oresat/oresat-proto-card/I2C-protection-sims/I2Cprotection.asc

C1: cap; .1µ
M1: pmos
R1: res; 10k
R2: res; 100k
R3: res; 1Meg
U1: LTC1441
V1: voltage; 1.2
V2: voltage; 3.3
V3: voltage; PULSE(0 3.3 0 0 0 5u 10u)
Named nets: 0, Vref, V+, Signal
.tran .001
