oresat/oresat-proto-card/a8-proto-card/cad-files/Connectors.kicad_sch

## KiCad design a8-proto-card/cad-files/Connectors.kicad_sch (2021-11-15)

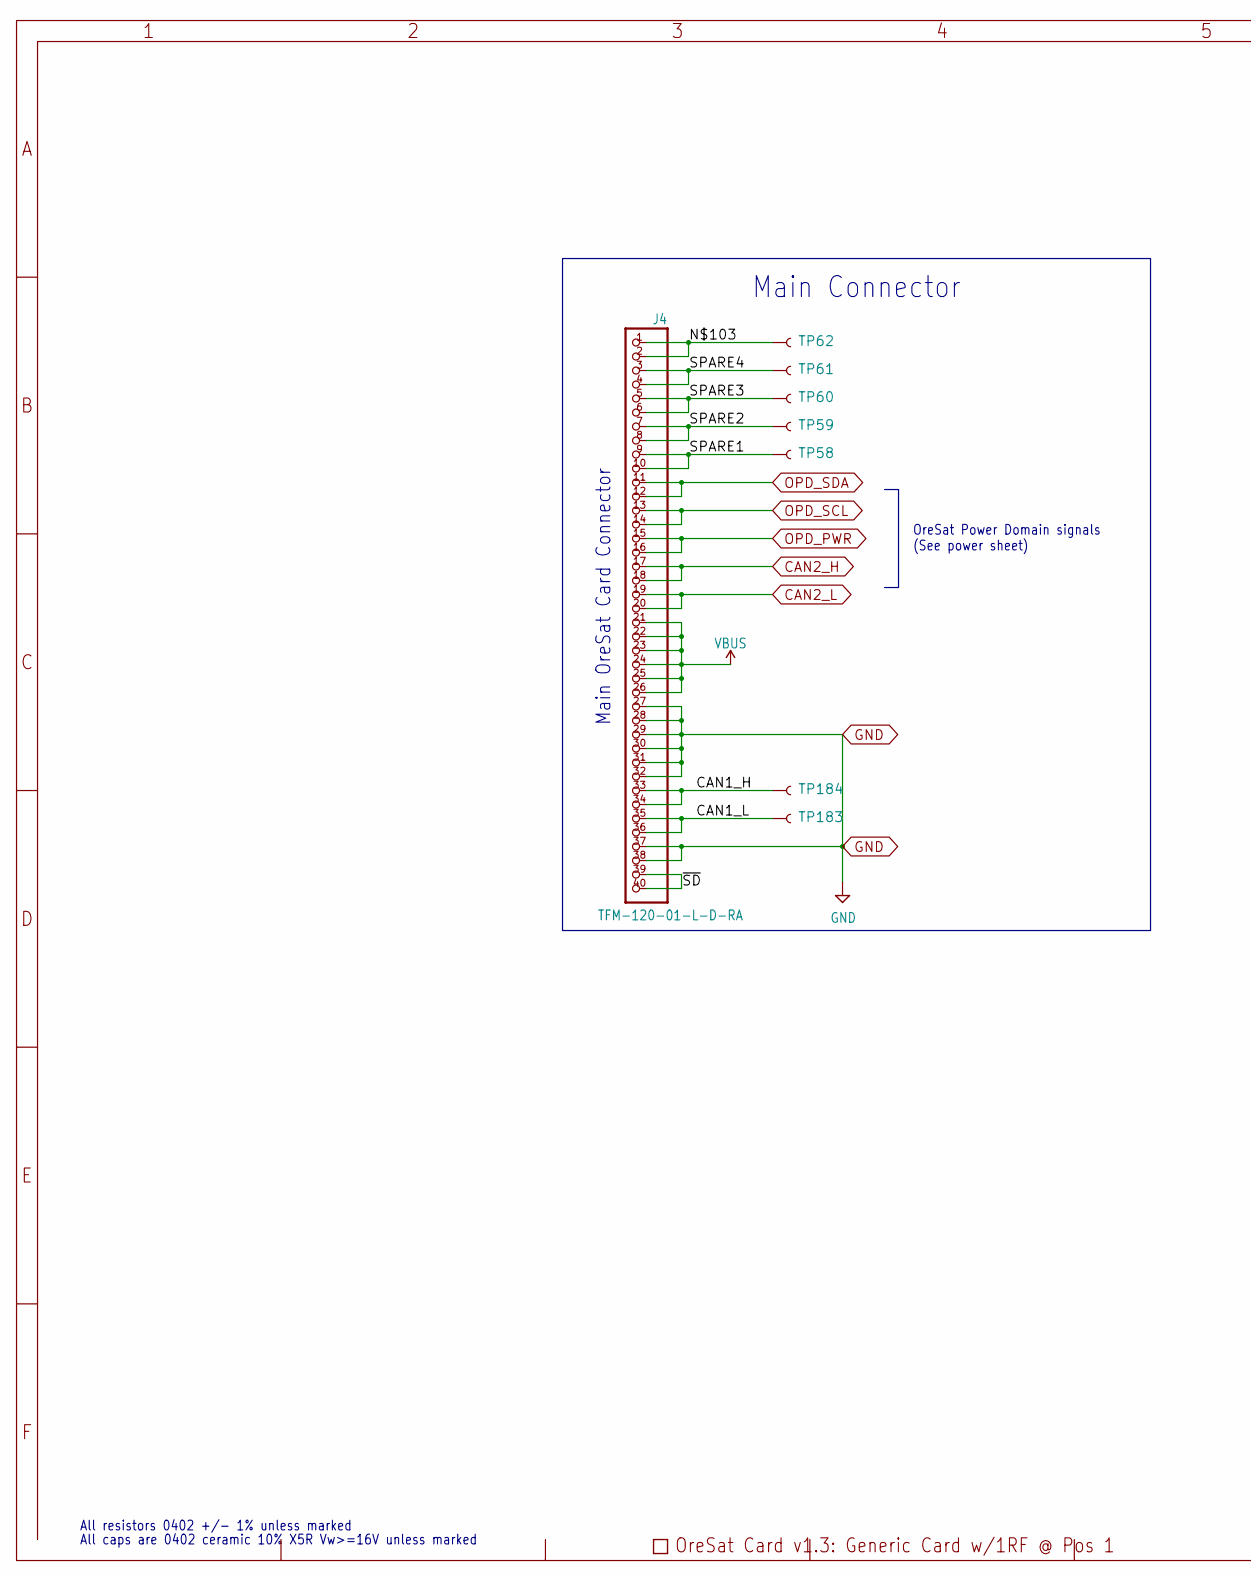
[picture p10: schematic Connectors.kicad_sch, part in row 1, column 1]

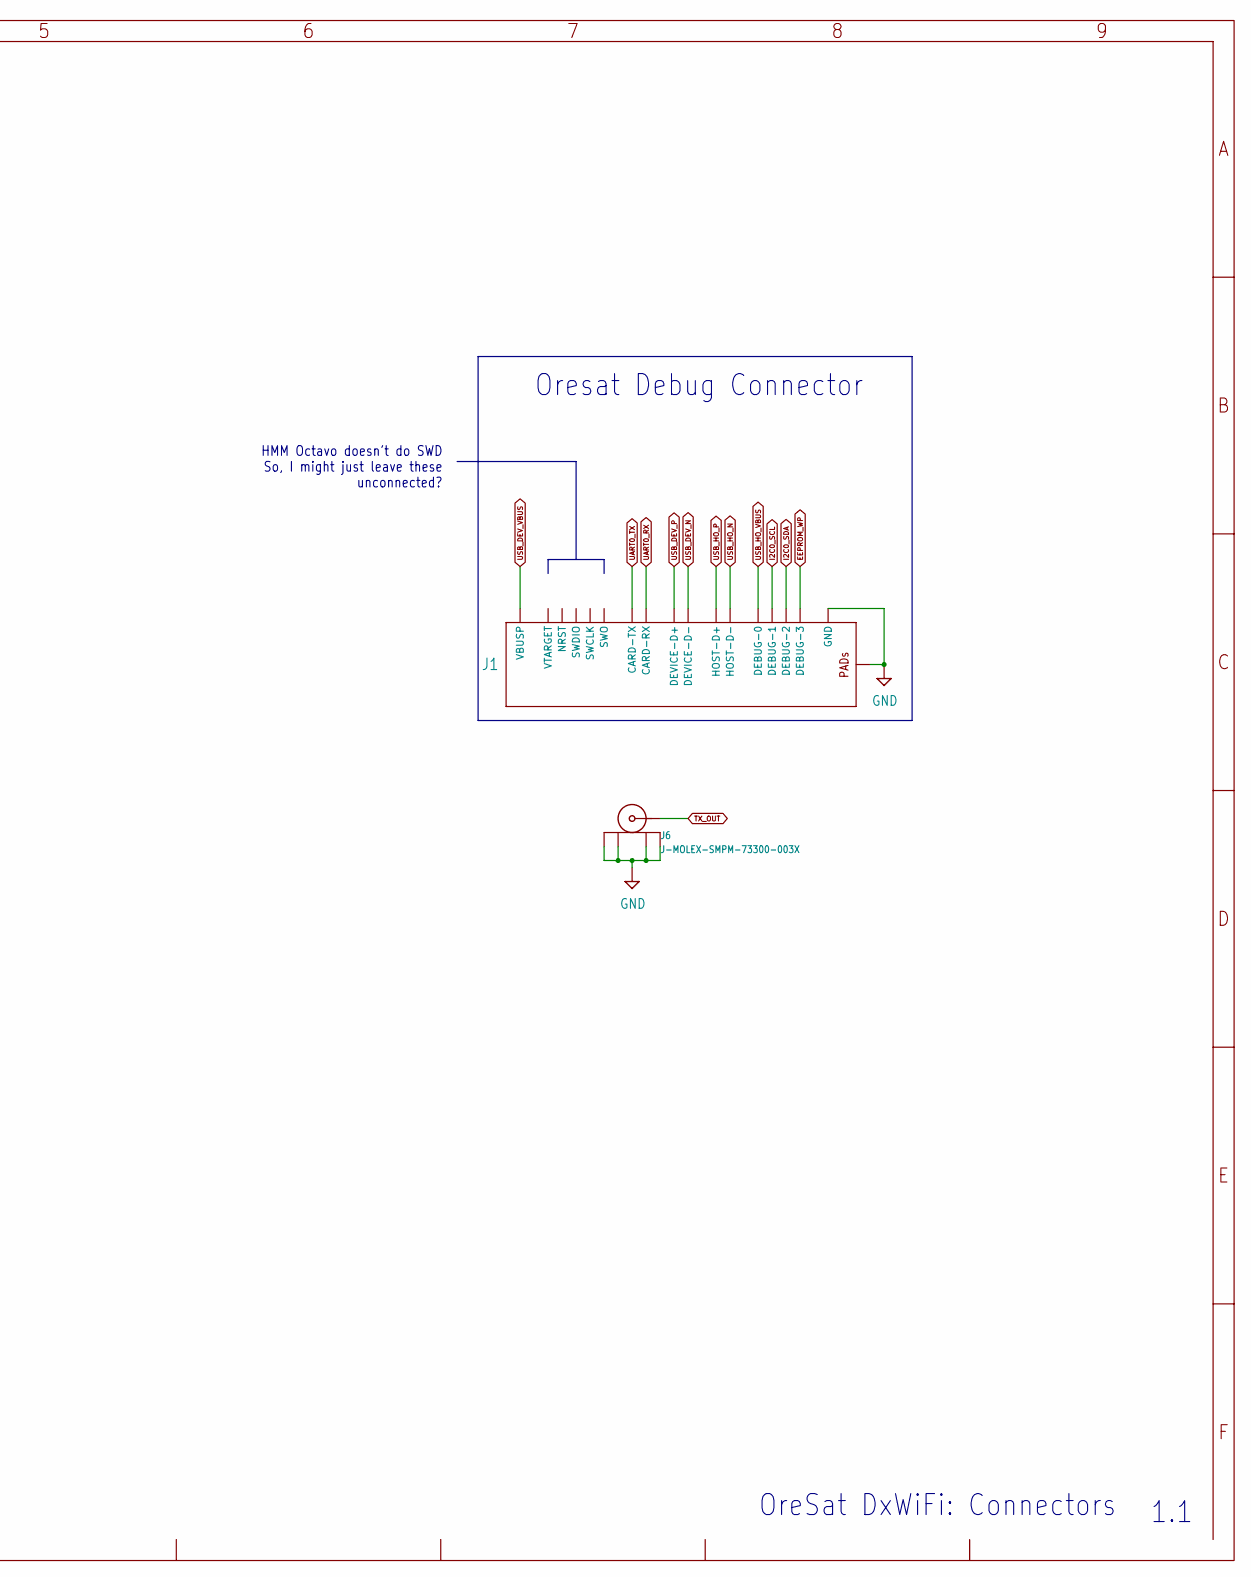
[picture p11: schematic Connectors.kicad_sch, part in row 1, column 2]

Parts:
J1: ORESAT-DEBUG-CONNECTOR-CARD; TE_2-1734592-0
J4: TFM-120-01-L-D-RA; J-SAMTEC-TFM-120-X1-XXX-D-RA
J6: J-MOLEX-SMPM-73300-003X; J-MOLEX-SMPM-073300-003X
PCB1: ORESAT-CARD-V1.3-GENERIC-1RF-POS1
TP58, TP59, TP60, TP61, TP62, TP183, TP184: TEST-POINT3X4; PAD.03X.04

Connections:
CAN1_H: J4.33, J4.34, TP184.1
CAN1_L: J4.35, J4.36, TP183.1
CAN2_H: J4.17, J4.18
CAN2_L: J4.19, J4.20
EEPROM_WP: J1.20 (DEBUG-3)
GND: J1.3 (GND), J1.6 (GND), J1.9 (GND), J1.PAD1 (PAD), J1.PAD2 (PAD), J4.27, J4.28, J4.29, J4.30, J4.31, J4.32, J4.37, J4.38, J6.P$1 (SHIELD3), J6.P$2 (SHIELD2), J6.P$3 (SHIELD1), J6.P$4 (SHIELD)
I2C0_SCL: J1.18 (DEBUG-1)
I2C0_SDA: J1.19 (DEBUG-2)
unnamed: J4.1, J4.2, TP62.1
OPD_PWR: J4.15, J4.16
OPD_SCL: J4.13, J4.14
OPD_SDA: J4.11, J4.12
SPARE1: J4.9, J4.10, TP58.1
SPARE2: J4.7, J4.8, TP59.1
SPARE3: J4.5, J4.6, TP60.1
SPARE4: J4.3, J4.4, TP61.1
TX_OUT: J6.RF (CENTER)
UART0_RX: J1.12 (CARD-RX)
UART0_TX: J1.13 (CARD-TX)
USB_DEV_N: J1.5 (DEVICE-D-)
USB_DEV_P: J1.4 (DEVICE-D+)
USB_DEV_VBUS: J1.1 (VBUSP), J1.2 (VBUSP)
USB_HO_N: J1.8 (HOST-D-)
USB_HO_P: J1.7 (HOST-D+)
USB_HO_VBUS: J1.17 (DEBUG-0)
VBUS: J4.21, J4.22, J4.23, J4.24, J4.25, J4.26
~SD: J4.39, J4.40

Notes on the sheet:
Main OreSat Card Connector
Oresat Debug Connector
OreSat DxWiFi: Connectors
HMM Octavo doesn't do SWD So, I might just leave these unconnected?
Main Connector
1.1
OreSat Power Domain signals (See power sheet)
All caps are 0402 ceramic 10% X5R Vw>=16V unless marked
All resistors 0402 +/- 1% unless marked
