oresat/oresat-proto-card/a8-proto-card/cad-files/OSD3358_PWR,_ETC._%3a_SIP_A,_E,_F.kicad_sch

## KiCad design a8-proto-card/cad-files/OSD3358_PWR,_ETC._%3a_SIP_A,_E,_F.kicad_sch (2021-11-15)

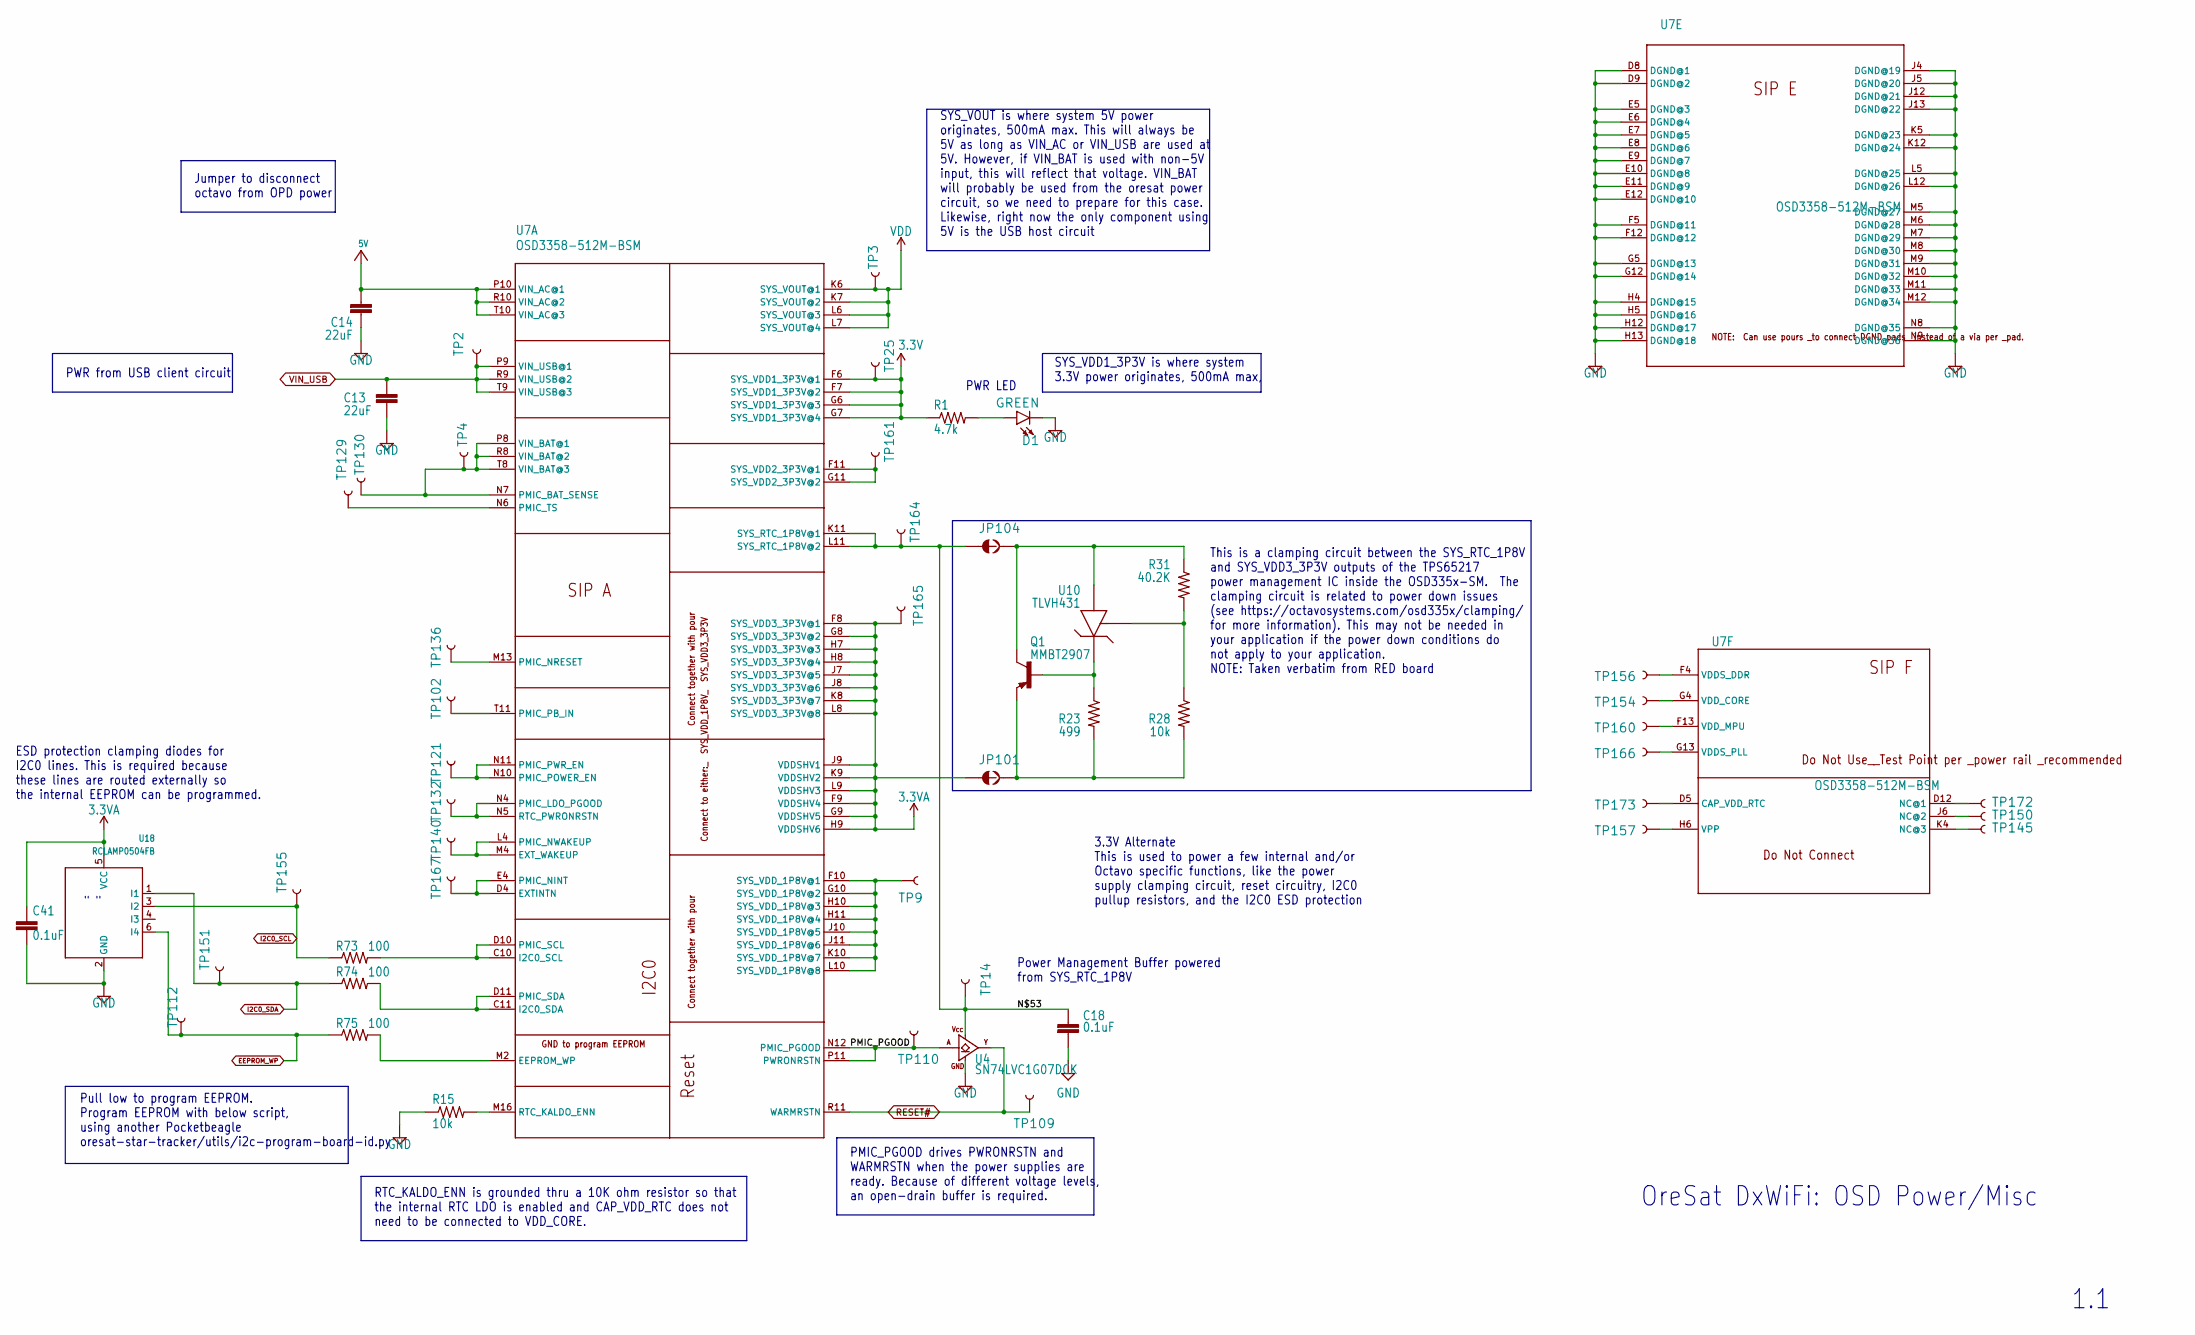
[picture p12: schematic OSD3358_PWR,_ETC._%3a_SIP_A,_E,_F.kicad_sch]

Parts:
C13, C14: 22uF; C1210
C18, C41: 0.1uF; .0603-A
D1: 150060VS55040; LED-0603
JP101, JP104: JUMPER-SMT_2_NC_TRACE_SILK; SMT-JUMPER_2_NC_TRACE_SILK
Q1: MMBT2907; SOT23-BEC
R1: 4.7k; .0603-A
R15, R28: 10k; .0603-A
R23: 499; .0603-A
R31: 40.2K; .0603-A
R73, R74, R75: 100; .0603-A
TP2, TP3, TP4, TP9, TP14, TP25, TP102, TP109, TP110, TP112, TP121, TP129, TP130, TP132, TP136, TP140, TP145, TP150, TP151, TP154, TP155, TP156, TP157, TP160, TP161, TP164, TP165, TP166, TP167, TP172, TP173: TEST-POINT3X4; PAD.03X.04
U4: SN74LVC1G07DCK; C70(TI-DCK)
U7: OSD3358-512M-BSM; OSD335X-BGA-256
U10: TLVH431; SOT23-3
U18: RCLAMP0504FB; SC70-6

Connections:
3.3V: R1.1, TP25.1, U7.F6 (SYS_VDD1_3P3V@1), U7.F7 (SYS_VDD1_3P3V@2), U7.G6 (SYS_VDD1_3P3V@3), U7.G7 (SYS_VDD1_3P3V@4)
3.3VA: C41.1, JP101.1, TP165.1, U7.F8 (SYS_VDD3_3P3V@1), U7.F9 (VDDSHV4), U7.G8 (SYS_VDD3_3P3V@2), U7.G9 (VDDSHV5), U7.H7 (SYS_VDD3_3P3V@3), U7.H8 (SYS_VDD3_3P3V@4), U7.H9 (VDDSHV6), U7.J7 (SYS_VDD3_3P3V@5), U7.J8 (SYS_VDD3_3P3V@6), U7.J9 (VDDSHV1), U7.K8 (SYS_VDD3_3P3V@7), U7.K9 (VDDSHV2), U7.L8 (SYS_VDD3_3P3V@8), U7.L9 (VDDSHV3), U18.5 (VCC)
5V: C14.1, U7.P10 (VIN_AC@1), U7.R10 (VIN_AC@2), U7.T10 (VIN_AC@3)
EEPROM_WP: R75.1, TP112.1, U18.6 (I4)
GND: C13.2, C14.2, C18.2, C41.2, D1.C, R15.1, U4.3 (GND), U7.D8 (DGND@1), U7.D9 (DGND@2), U7.E5 (DGND@3), U7.E6 (DGND@4), U7.E7 (DGND@5), U7.E8 (DGND@6), U7.E9 (DGND@7), U7.E10 (DGND@8), U7.E11 (DGND@9), U7.E12 (DGND@10), U7.F5 (DGND@11), U7.F12 (DGND@12), U7.G5 (DGND@13), U7.G12 (DGND@14), U7.H4 (DGND@15), U7.H5 (DGND@16), U7.H12 (DGND@17), U7.H13 (DGND@18), U7.J4 (DGND@19), U7.J5 (DGND@20), U7.J12 (DGND@21), U7.J13 (DGND@22), U7.K5 (DGND@23), U7.K12 (DGND@24), U7.L5 (DGND@25), U7.L12 (DGND@26), U7.M5 (DGND@27), U7.M6 (DGND@28), U7.M7 (DGND@29), U7.M8 (DGND@30), U7.M9 (DGND@31), U7.M10 (DGND@32), U7.M11 (DGND@33), U7.M12 (DGND@34), U7.N8 (DGND@35), U7.N9 (DGND@36), U18.2 (GND)
I2C0_SCL: R73.1, TP155.1, U18.3 (I2)
I2C0_SDA: R74.1, TP151.1, U18.1 (I1)
unnamed: C18.1, JP104.1, TP14.1, TP164.1, U4.5 (VCC), U7.K11 (SYS_RTC_1P8V@1), U7.L11 (SYS_RTC_1P8V@2)
unnamed: D1.A, R1.2
unnamed: JP101.2, Q1.E, R23.2, R28.2
unnamed: JP104.2, Q1.C, R31.1, U10.3 (ANODE)
unnamed: Q1.B, R23.1, U10.2 (CATHODE)
unnamed: R15.2, U7.M16 (RTC_KALDO_ENN)
unnamed: R28.1, R31.2, U10.1 (REF)
unnamed: R73.2, U7.C10 (I2C0_SCL), U7.D10 (PMIC_SCL)
unnamed: R74.2, U7.C11 (I2C0_SDA), U7.D11 (PMIC_SDA)
unnamed: R75.2, U7.M2 (EEPROM_WP)
unnamed: TP9.1, U7.F10 (SYS_VDD_1P8V@1), U7.G10 (SYS_VDD_1P8V@2), U7.H10 (SYS_VDD_1P8V@3), U7.H11 (SYS_VDD_1P8V@4), U7.J10 (SYS_VDD_1P8V@5), U7.J11 (SYS_VDD_1P8V@6), U7.K10 (SYS_VDD_1P8V@7), U7.L10 (SYS_VDD_1P8V@8)
unnamed: TP102.1, U7.T11 (PMIC_PB_IN)
unnamed: TP121.1, U7.N10 (PMIC_POWER_EN), U7.N11 (PMIC_PWR_EN)
unnamed: TP129.1, U7.N6 (PMIC_TS)
unnamed: TP4.1, TP130.1, U7.N7 (PMIC_BAT_SENSE), U7.P8 (VIN_BAT@1), U7.R8 (VIN_BAT@2), U7.T8 (VIN_BAT@3)
unnamed: TP132.1, U7.N4 (PMIC_LDO_PGOOD), U7.N5 (RTC_PWRONRSTN)
unnamed: TP136.1, U7.M13 (PMIC_NRESET)
unnamed: TP140.1, U7.L4 (PMIC_NWAKEUP), U7.M4 (EXT_WAKEUP)
unnamed: TP145.1, U7.K4 (NC@3)
unnamed: TP150.1, U7.J6 (NC@2)
unnamed: TP154.1, U7.G4 (VDD_CORE)
unnamed: TP156.1, U7.F4 (VDDS_DDR)
unnamed: TP157.1, U7.H6 (VPP)
unnamed: TP160.1, U7.F13 (VDD_MPU)
unnamed: TP161.1, U7.F11 (SYS_VDD2_3P3V@1), U7.G11 (SYS_VDD2_3P3V@2)
unnamed: TP166.1, U7.G13 (VDDS_PLL)
unnamed: TP167.1, U7.D4 (EXTINTN), U7.E4 (PMIC_NINT)
unnamed: TP172.1, U7.D12 (NC@1)
unnamed: TP173.1, U7.D5 (CAP_VDD_RTC)
PMIC_PGOOD: TP110.1, U4.2 (A), U7.N12 (PMIC_PGOOD), U7.P11 (PWRONRSTN)
RESET#: TP109.1, U4.4 (Y), U7.R11 (WARMRSTN)
VDD: TP3.1, U7.K6 (SYS_VOUT@1), U7.K7 (SYS_VOUT@2), U7.L6 (SYS_VOUT@3), U7.L7 (SYS_VOUT@4)
VIN_USB: C13.1, TP2.1, U7.P9 (VIN_USB@1), U7.R9 (VIN_USB@2), U7.T9 (VIN_USB@3)

Notes on the sheet:
Pull low to program EEPROM. Program EEPROM with below script, using another Pocketbeagle oresat-star-tracker/utils/i2c-program-board-id.py
ESD protection clamping diodes for I2C0 lines. This is required because these lines are routed externally so the internal EEPROM can be programmed.
This is a clamping circuit between the SYS_RTC_1P8V and SYS_VDD3_3P3V outputs of the TPS65217 power management IC inside the OSD335x-SM. The clamping circuit is related to power down issues (see https://octavosystems.com/osd335x/clamping/ for more information). This may not be needed in your applic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
RTC_KALDO_ENN is grounded thru a 10K ohm resistor so that the internal RTC LDO is enabled and CAP_VDD_RTC does not need to be connected to VDD_CORE.
3.3V Alternate This is used to power a few internal and/or Octavo specific functions, like the power supply clamping circuit, reset circuitry, I2C0 pullup resistors, and the I2C0 ESD protection
Jumper to disconnect octavo from OPD power
SYS_VDD1_3P3V is where system 3.3V power originates, 500mA max,
" "
PMIC_PGOOD drives PWRONRSTN and WARMRSTN when the power supplies are ready. Because of different voltage levels, an open-drain buffer is required.
OreSat DxWiFi: OSD Power/Misc
SYS_VOUT is where system 5V power originates, 500mA max. This will always be 5V as long as VIN_AC or VIN_USB are used at 5V. However, if VIN_BAT is used with non-5V input, this will reflect that voltage. VIN_BAT will probably be used from the oresat power circuit, so we need to prepare for this cas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
Power Management Buffer powered from SYS_RTC_1P8V
PWR from USB client circuit
1.1
PWR LED
