oresat/oresat-proto-card/a8-proto-card/cad-files/OSD3358_SD,_eMMC%3a_SIP_C,_D.kicad_sch

## KiCad design a8-proto-card/cad-files/OSD3358_SD,_eMMC%3a_SIP_C,_D.kicad_sch (2021-11-15)

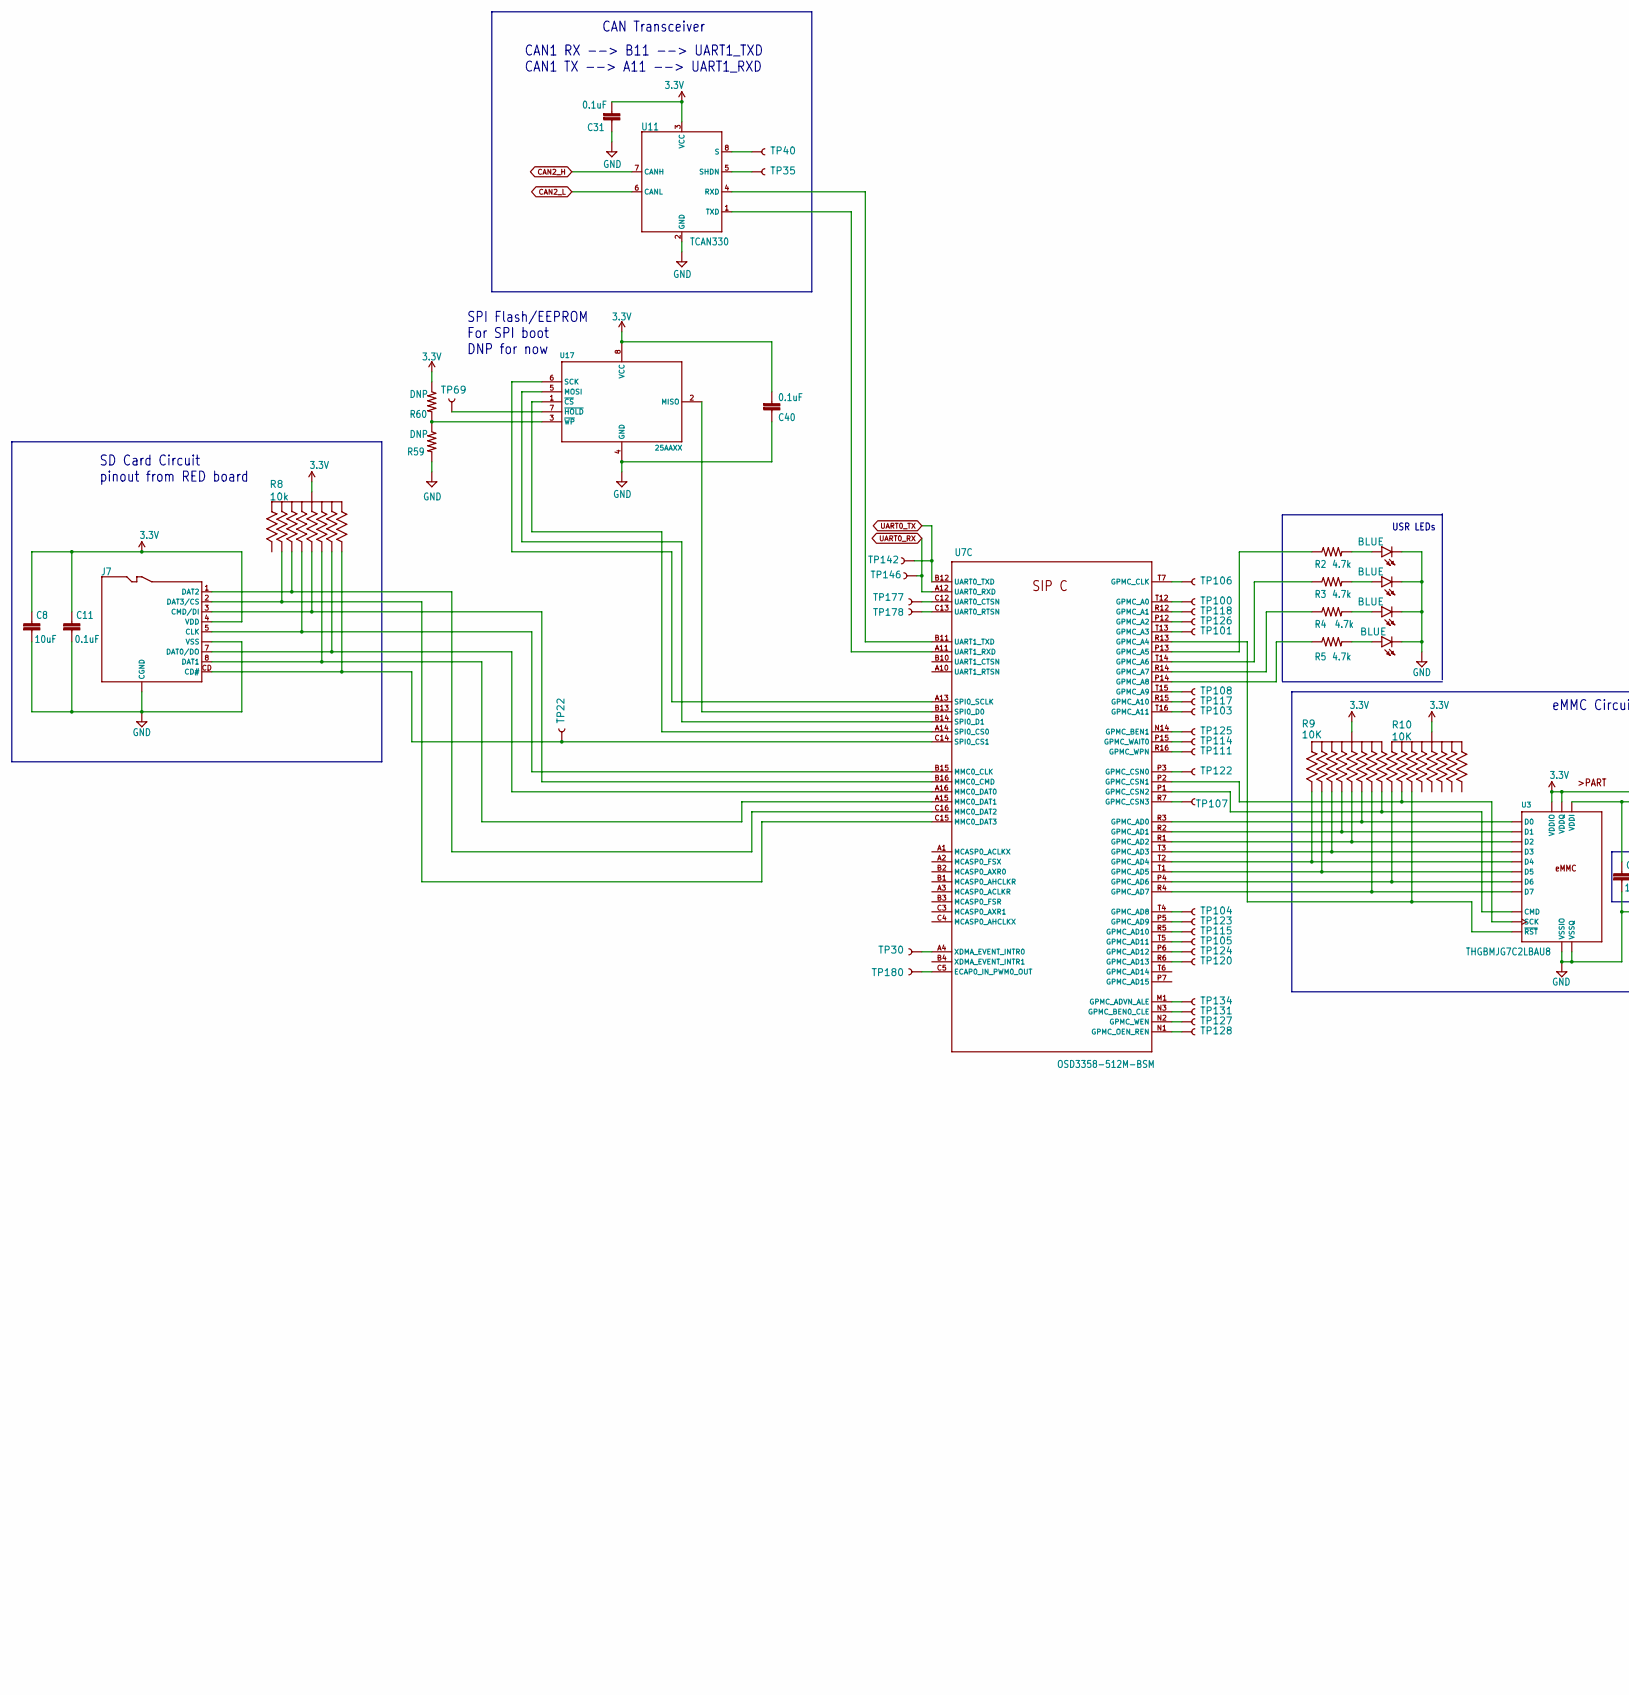
[picture p13: schematic OSD3358_SD,_eMMC%3a_SIP_C,_D.kicad_sch, part in row 1, column 1]

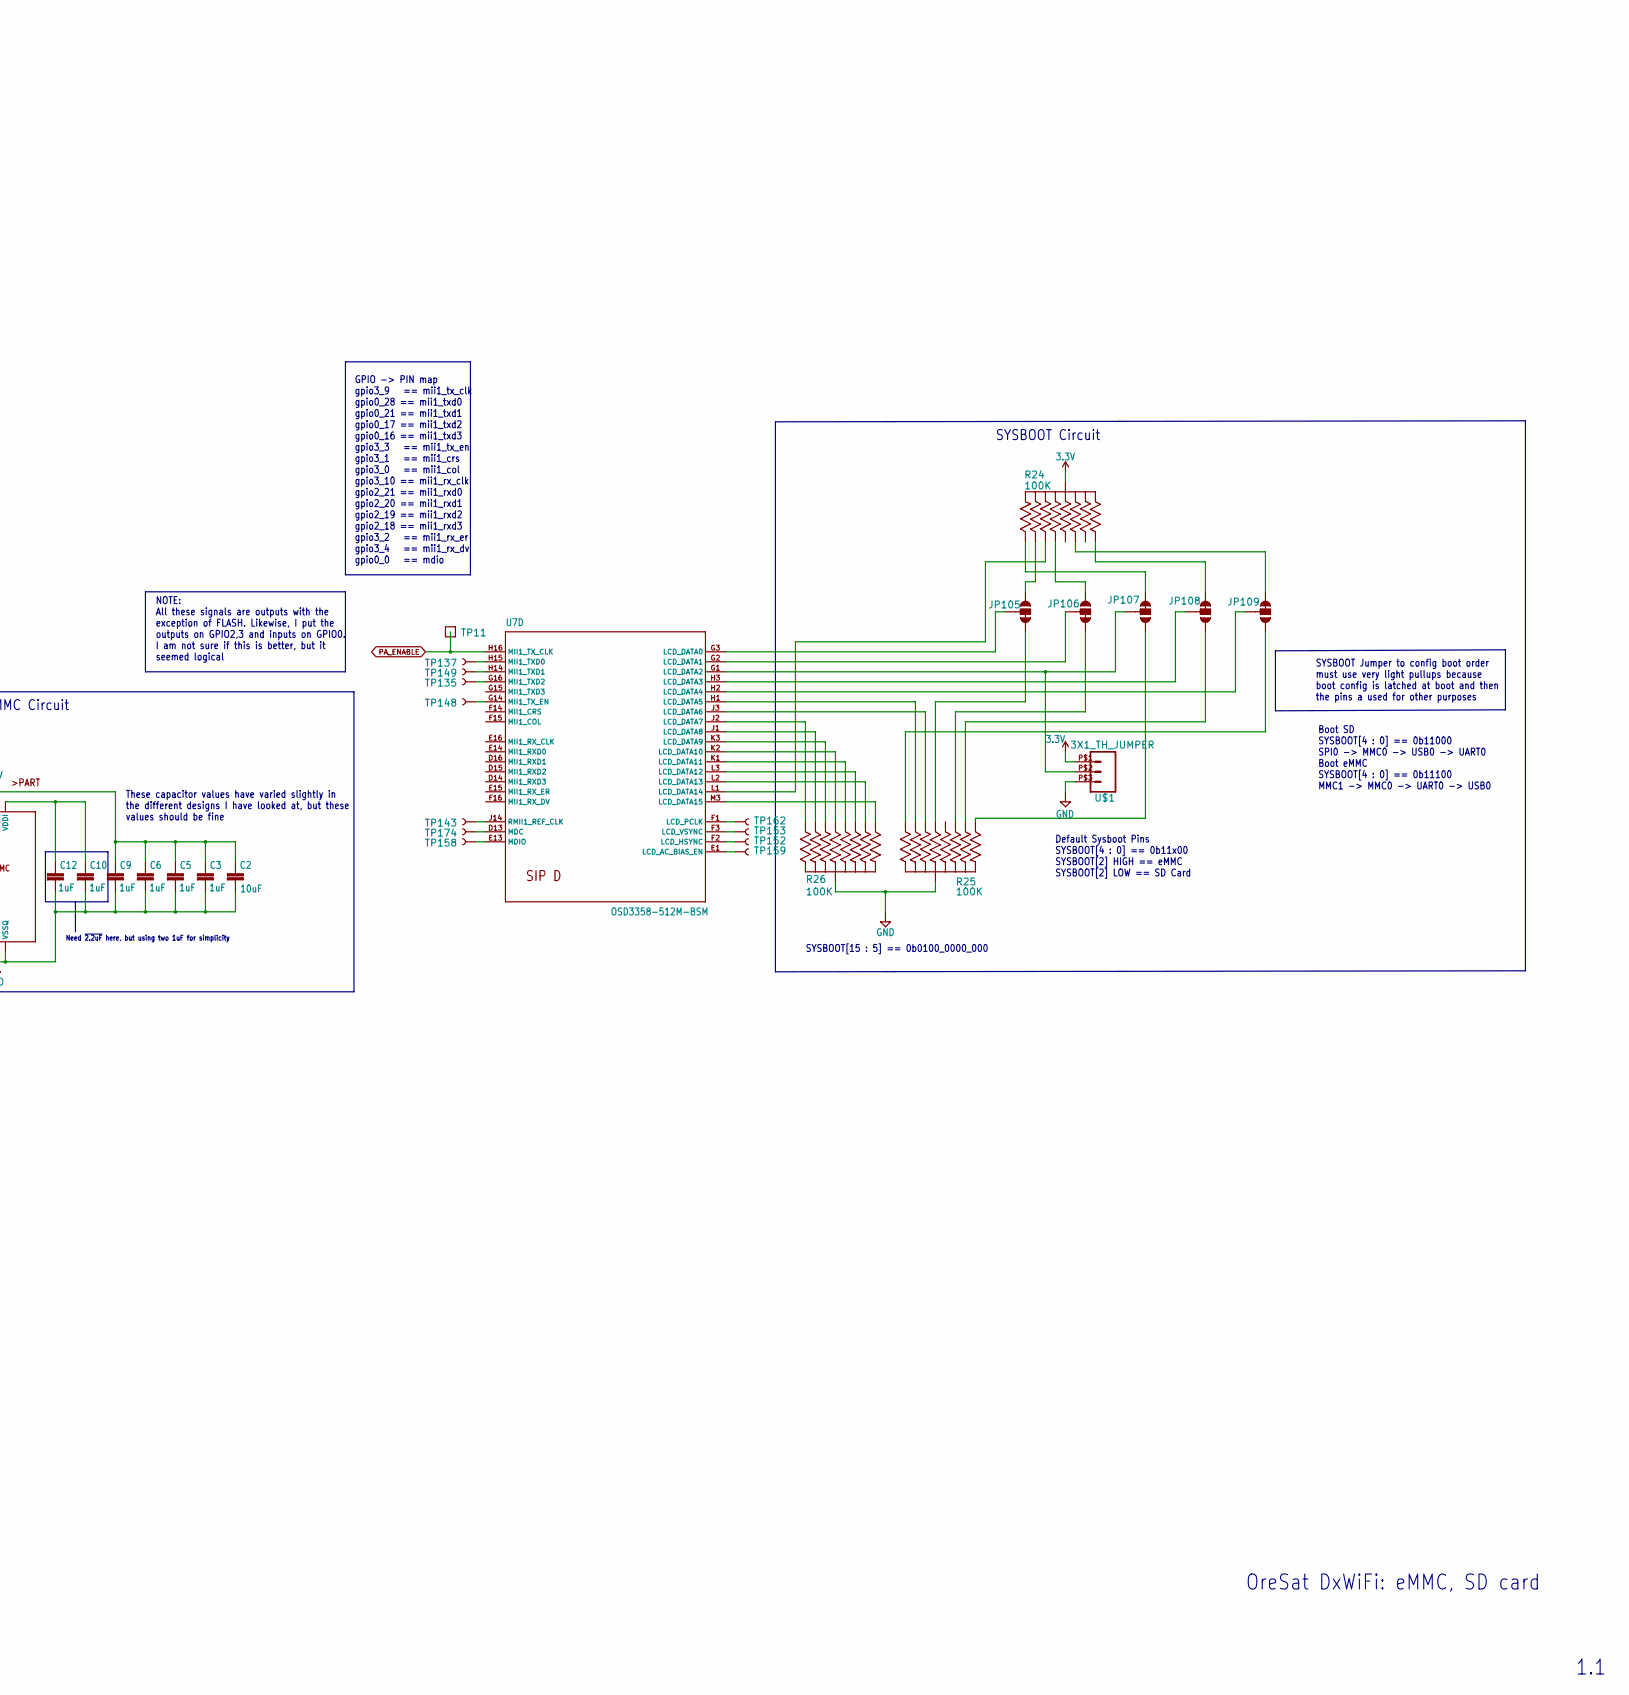
[picture p14: schematic OSD3358_SD,_eMMC%3a_SIP_C,_D.kicad_sch, part in row 1, column 2]

Parts:
C2, C8: 10uF; .0805-B
C3, C5, C6, C9, C10, C12: 1uF; .0603-A
C11, C31, C40: 0.1uF; .0603-A
D2, D3, D4, D5: BLUE; LED-0603
J7: DM3BT-DSF-PEJS
JP105, JP106, JP107, JP108, JP109: JUMPER-SMT_3_1-NC_TRACE_SILK; SMT-JUMPER_3_1-NC_TRACE_SILK
R2, R3, R4, R5: 4.7k; .0603-A
R8: 10K; ARRAY_EXBA-M
R9, R10: EXB-A10P103J; ARRAY_EXBA-M
R24, R25, R26: EXB-A10P104J; ARRAY_EXBA-M
R59, R60: DNP; .0603-A
TP11: TEST-POINT; 2MM-TEST-POINT
TP22, TP30, TP35, TP40, TP69, TP100, TP101, TP103, TP104, TP105, TP106, TP107, TP108, TP111, TP114, TP115, TP117, TP118, TP120, TP122, TP123, TP124, TP125, TP126, TP127, TP128, TP131, TP134, TP135, TP137, TP142, TP143, TP146, TP148, TP149, TP152, TP153, TP158, TP159, TP162, TP174, TP177, TP178, TP180: TEST-POINT3X4; PAD.03X.04
U3: THGBMJG7C2LBAU8; BGA-153(11.5X13)(EMMC-BA)
U7: OSD3358-512M-BSM; OSD335X-BGA-256
U11: TCAN330; SOT23-8_TI-DCN
U17: 25AAXX; SOIC8
U$1: 3X1_TH_JUMPER; 3X1

Connections:
3.3V: C2.1, C3.1, C5.1, C6.1, C8.1, C9.1, C11.1, C31.2, C40.2, J7.4 (VDD), R8.5 (55), R8.10 (55), R9.5 (55), R9.10 (55), R10.5 (55), R10.10 (55), R24.5 (55), R24.10 (55), R60.1, U3.C6 (VDDQ), U3.E6 (VDDIO), U3.F5 (VDDIO), U3.J10 (VDDIO), U3.K9 (VDDIO), U3.M4 (VDDQ), U3.N4 (VDDQ), U3.P3 (VDDQ), U3.P5 (VDDQ), U11.3 (VCC), U17.8 (VCC), U$1.P$1 (1)
CAN2_H: U11.7 (CANH)
CAN2_L: U11.6 (CANL)
GND: C2.2, C3.2, C5.2, C6.2, C8.2, C9.2, C10.2, C11.2, C12.2, C31.1, C40.1, D2.C, D3.C, D4.C, D5.C, J7.6 (VSS), J7.CGND1 (CGND), J7.CGND2 (CGND), J7.CGND3 (CGND), J7.CGND4 (CGND), J7.CGND5 (CGND), J7.CGND6 (CGND), J7.GND (VSS), R25.5 (55), R25.10 (55), R26.5 (55), R26.10 (55), R59.2, U3.A6 (VSSIO), U3.C4 (VSSQ), U3.E7 (VSSIO), U3.G5 (VSSIO), U3.H10 (VSSIO), U3.J5 (VSSIO), U3.K8 (VSSIO), U3.N2 (VSSQ), U3.N5 (VSSQ), U3.P4 (VSSQ), U3.P6 (VSSQ), U11.2 (GND), U17.4 (GND), U$1.P$3 (3)
unnamed: C10.1, C12.1, U3.C2 (VDDI)
unnamed: D2.A, R2.2
unnamed: D3.A, R3.2
unnamed: D4.A, R4.2
unnamed: D5.A, R5.2
unnamed: J7.1 (DAT2), R8.2 (22), U7.C16 (MMC0_DAT2)
unnamed: J7.2 (DAT3/CS), R8.9 (99), U7.C15 (MMC0_DAT3)
unnamed: J7.3 (CMD/DI), R8.3 (33), U7.B16 (MMC0_CMD)
unnamed: J7.5 (CLK), R8.8 (88), U7.B15 (MMC0_CLK)
unnamed: J7.7 (DAT0/DO), R8.4 (44), U7.A16 (MMC0_DAT0)
unnamed: J7.8 (DAT1), R8.7 (77), U7.A15 (MMC0_DAT1)
unnamed: J7.CD (CD#), R8.6 (66), TP22.1, U7.C14 (SPI0_CS1)
unnamed: JP105.1, R24.9 (99)
unnamed: JP105.2, U7.G3 (LCD_DATA0)
unnamed: JP105.3, R25.3 (33)
unnamed: JP106.1, R24.8 (88)
unnamed: JP106.2, U7.G2 (LCD_DATA1)
unnamed: JP106.3, R25.2 (22)
unnamed: JP107.1, R25.1 (11)
unnamed: JP107.2, U7.G1 (LCD_DATA2), U$1.P$2 (2)
unnamed: JP107.3, R24.1 (11)
unnamed: JP108.1, R25.9 (99)
unnamed: JP108.2, U7.H3 (LCD_DATA3)
unnamed: JP108.3, R24.6 (66)
unnamed: JP109.1, R25.6 (66)
unnamed: JP109.2, U7.H2 (LCD_DATA4)
unnamed: JP109.3, R24.7 (77)
unnamed: R2.1, U7.P13 (GPMC_A5)
unnamed: R3.1, U7.T14 (GPMC_A6)
unnamed: R4.1, U7.R14 (GPMC_A7)
unnamed: R5.1, U7.P14 (GPMC_A8)
unnamed: R9.1 (11), U3.B3 (D4), U7.T2 (GPMC_AD4)
unnamed: R9.2 (22), U3.B2 (D3), U7.T3 (GPMC_AD3)
unnamed: R9.3 (33), U3.A5 (D2), U7.R1 (GPMC_AD2)
unnamed: R9.4 (44), U3.B6 (D7), U7.R4 (GPMC_AD7)
unnamed: R9.6 (66), U3.M5 (CMD), U7.P1 (GPMC_CSN2)
unnamed: R9.7 (77), U3.A3 (D0), U7.R3 (GPMC_AD0)
unnamed: R9.8 (88), U3.A4 (D1), U7.R2 (GPMC_AD1)
unnamed: R9.9 (99), U3.B4 (D5), U7.T1 (GPMC_AD5)
unnamed: R10.1 (11), U3.B5 (D6), U7.P4 (GPMC_AD6)
unnamed: R10.2 (22), U3.K5 (~RST), U7.R13 (GPMC_A4)
unnamed: R10.9 (99), U3.M6 (SCK), U7.P2 (GPMC_CSN1)
unnamed: R24.2 (22), U7.L1 (LCD_DATA14)
unnamed: R25.4 (44), U7.H1 (LCD_DATA5)
unnamed: R25.7 (77), U7.J3 (LCD_DATA6)
unnamed: R26.1 (11), U7.M3 (LCD_DATA15)
unnamed: R26.2 (22), U7.L3 (LCD_DATA12)
unnamed: R26.3 (33), U7.K2 (LCD_DATA10)
unnamed: R26.4 (44), U7.J1 (LCD_DATA8)
unnamed: R26.6 (66), U7.J2 (LCD_DATA7)
unnamed: R26.7 (77), U7.K3 (LCD_DATA9)
unnamed: R26.8 (88), U7.K1 (LCD_DATA11)
unnamed: R26.9 (99), U7.L2 (LCD_DATA13)
unnamed: R59.1, R60.2, U17.3 (~WP)
unnamed: TP30.1, U7.A4 (XDMA_EVENT_INTR0)
unnamed: TP35.1, U11.5 (SHDN)
unnamed: TP40.1, U11.8 (S)
unnamed: TP69.1, U17.7 (~HOLD)
unnamed: TP100.1, U7.T12 (GPMC_A0)
unnamed: TP101.1, U7.T13 (GPMC_A3)
unnamed: TP103.1, U7.T16 (GPMC_A11)
unnamed: TP104.1, U7.T4 (GPMC_AD8)
unnamed: TP105.1, U7.T5 (GPMC_AD11)
unnamed: TP106.1, U7.T7 (GPMC_CLK)
unnamed: TP107.1, U7.R7 (GPMC_CSN3)
unnamed: TP108.1, U7.T15 (GPMC_A9)
unnamed: TP111.1, U7.R16 (GPMC_WPN)
unnamed: TP114.1, U7.P15 (GPMC_WAIT0)
unnamed: TP115.1, U7.R5 (GPMC_AD10)
unnamed: TP117.1, U7.R15 (GPMC_A10)
unnamed: TP118.1, U7.R12 (GPMC_A1)
unnamed: TP120.1, U7.R6 (GPMC_AD13)
unnamed: TP122.1, U7.P3 (GPMC_CSN0)
unnamed: TP123.1, U7.P5 (GPMC_AD9)
unnamed: TP124.1, U7.P6 (GPMC_AD12)
unnamed: TP125.1, U7.N14 (GPMC_BEN1)
unnamed: TP126.1, U7.P12 (GPMC_A2)
unnamed: TP127.1, U7.N2 (GPMC_WEN)
unnamed: TP128.1, U7.N1 (GPMC_OEN_REN)
unnamed: TP131.1, U7.N3 (GPMC_BEN0_CLE)
unnamed: TP134.1, U7.M1 (GPMC_ADVN_ALE)
unnamed: TP135.1, U7.G16 (MII1_TXD2)
unnamed: TP137.1, U7.H15 (MII1_TXD0)
unnamed: TP143.1, U7.J14 (RMII1_REF_CLK)
unnamed: TP148.1, U7.G14 (MII1_TX_EN)
unnamed: TP149.1, U7.H14 (MII1_TXD1)
unnamed: TP152.1, U7.F2 (LCD_HSYNC)
unnamed: TP153.1, U7.F3 (LCD_VSYNC)
unnamed: TP158.1, U7.E13 (MDIO)
unnamed: TP159.1, U7.E1 (LCD_AC_BIAS_EN)
unnamed: TP162.1, U7.F1 (LCD_PCLK)
unnamed: TP174.1, U7.D13 (MDC)
unnamed: TP177.1, U7.C12 (UART0_CTSN)
unnamed: TP178.1, U7.C13 (UART0_RTSN)
unnamed: TP180.1, U7.C5 (ECAP0_IN_PWM0_OUT)
unnamed: U7.A11 (UART1_RXD), U11.1 (TXD)
unnamed: U7.B11 (UART1_TXD), U11.4 (RXD)
unnamed: U7.A14 (SPI0_CS0), U17.1 (~CS)
unnamed: U7.B13 (SPI0_D0), U17.2 (MISO)
unnamed: U7.B14 (SPI0_D1), U17.5 (MOSI)
unnamed: U7.A13 (SPI0_SCLK), U17.6 (SCK)
PA_ENABLE: TP11.1, U7.H16 (MII1_TX_CLK)
UART0_RX: TP146.1, U7.A12 (UART0_RXD)
UART0_TX: TP142.1, U7.B12 (UART0_TXD)

Notes on the sheet:
CAN1 RX --> B11 --> UART1_TXD CAN1 TX --> A11 --> UART1_RXD
SD Card Circuit pinout from RED board
NOTE: All these signals are outputs with the exception of FLASH. Likewise, I put the outputs on GPIO2,3 and inputs on GPIO0. I am not sure if this is better, but it seemed logical
SPI Flash/EEPROM For SPI boot DNP for now
SYSBOOT Circuit
OreSat DxWiFi: eMMC, SD card
Default Sysboot Pins SYSBOOT[4 : 0] == 0b11x00 SYSBOOT[2] HIGH == eMMC SYSBOOT[2] LOW == SD Card
These capacitor values have varied slightly in the different designs I have looked at, but these values should be fine
SYSBOOT[15 : 5] == 0b0100_0000_000
Boot SD SYSBOOT[4 : 0] == 0b11000 SPI0 -> MMC0 -> USB0 -> UART0 Boot eMMC SYSBOOT[4 : 0] == 0b11100 MMC1 -> MMC0 -> UART0 -> USB0
GPIO -> PIN map gpio3_9 == mii1_tx_clk gpio0_28 == mii1_txd0 gpio0_21 == mii1_txd1 gpio0_17 == mii1_txd2 gpio0_16 == mii1_txd3 gpio3_3 == mii1_tx_en gpio3_1 == mii1_crs gpio3_0 == mii1_col gpio3_10 == mii1_rx_clk gpio2_21 == mii1_rxd0 gpio2_20 == mii1_rxd1 gpio2_19 == mii1_rxd2 gpio2_18 == mii1_rxd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
USR LEDs
SYSBOOT Jumper to config boot order must use very light pullups because boot config is latched at boot and then the pins a used for other purposes
Need ~{2.2uF} here, but using two 1uF for simplicity
1.1
CAN Transceiver
eMMC Circuit
