oresat/oresat-proto-card/a8-proto-card/cad-files/OSD3358_USB,_JTAG,_XTAL,_etc_%3a_SIP_B.kicad_sch

## KiCad design a8-proto-card/cad-files/OSD3358_USB,_JTAG,_XTAL,_etc_%3a_SIP_B.kicad_sch (2021-11-15)

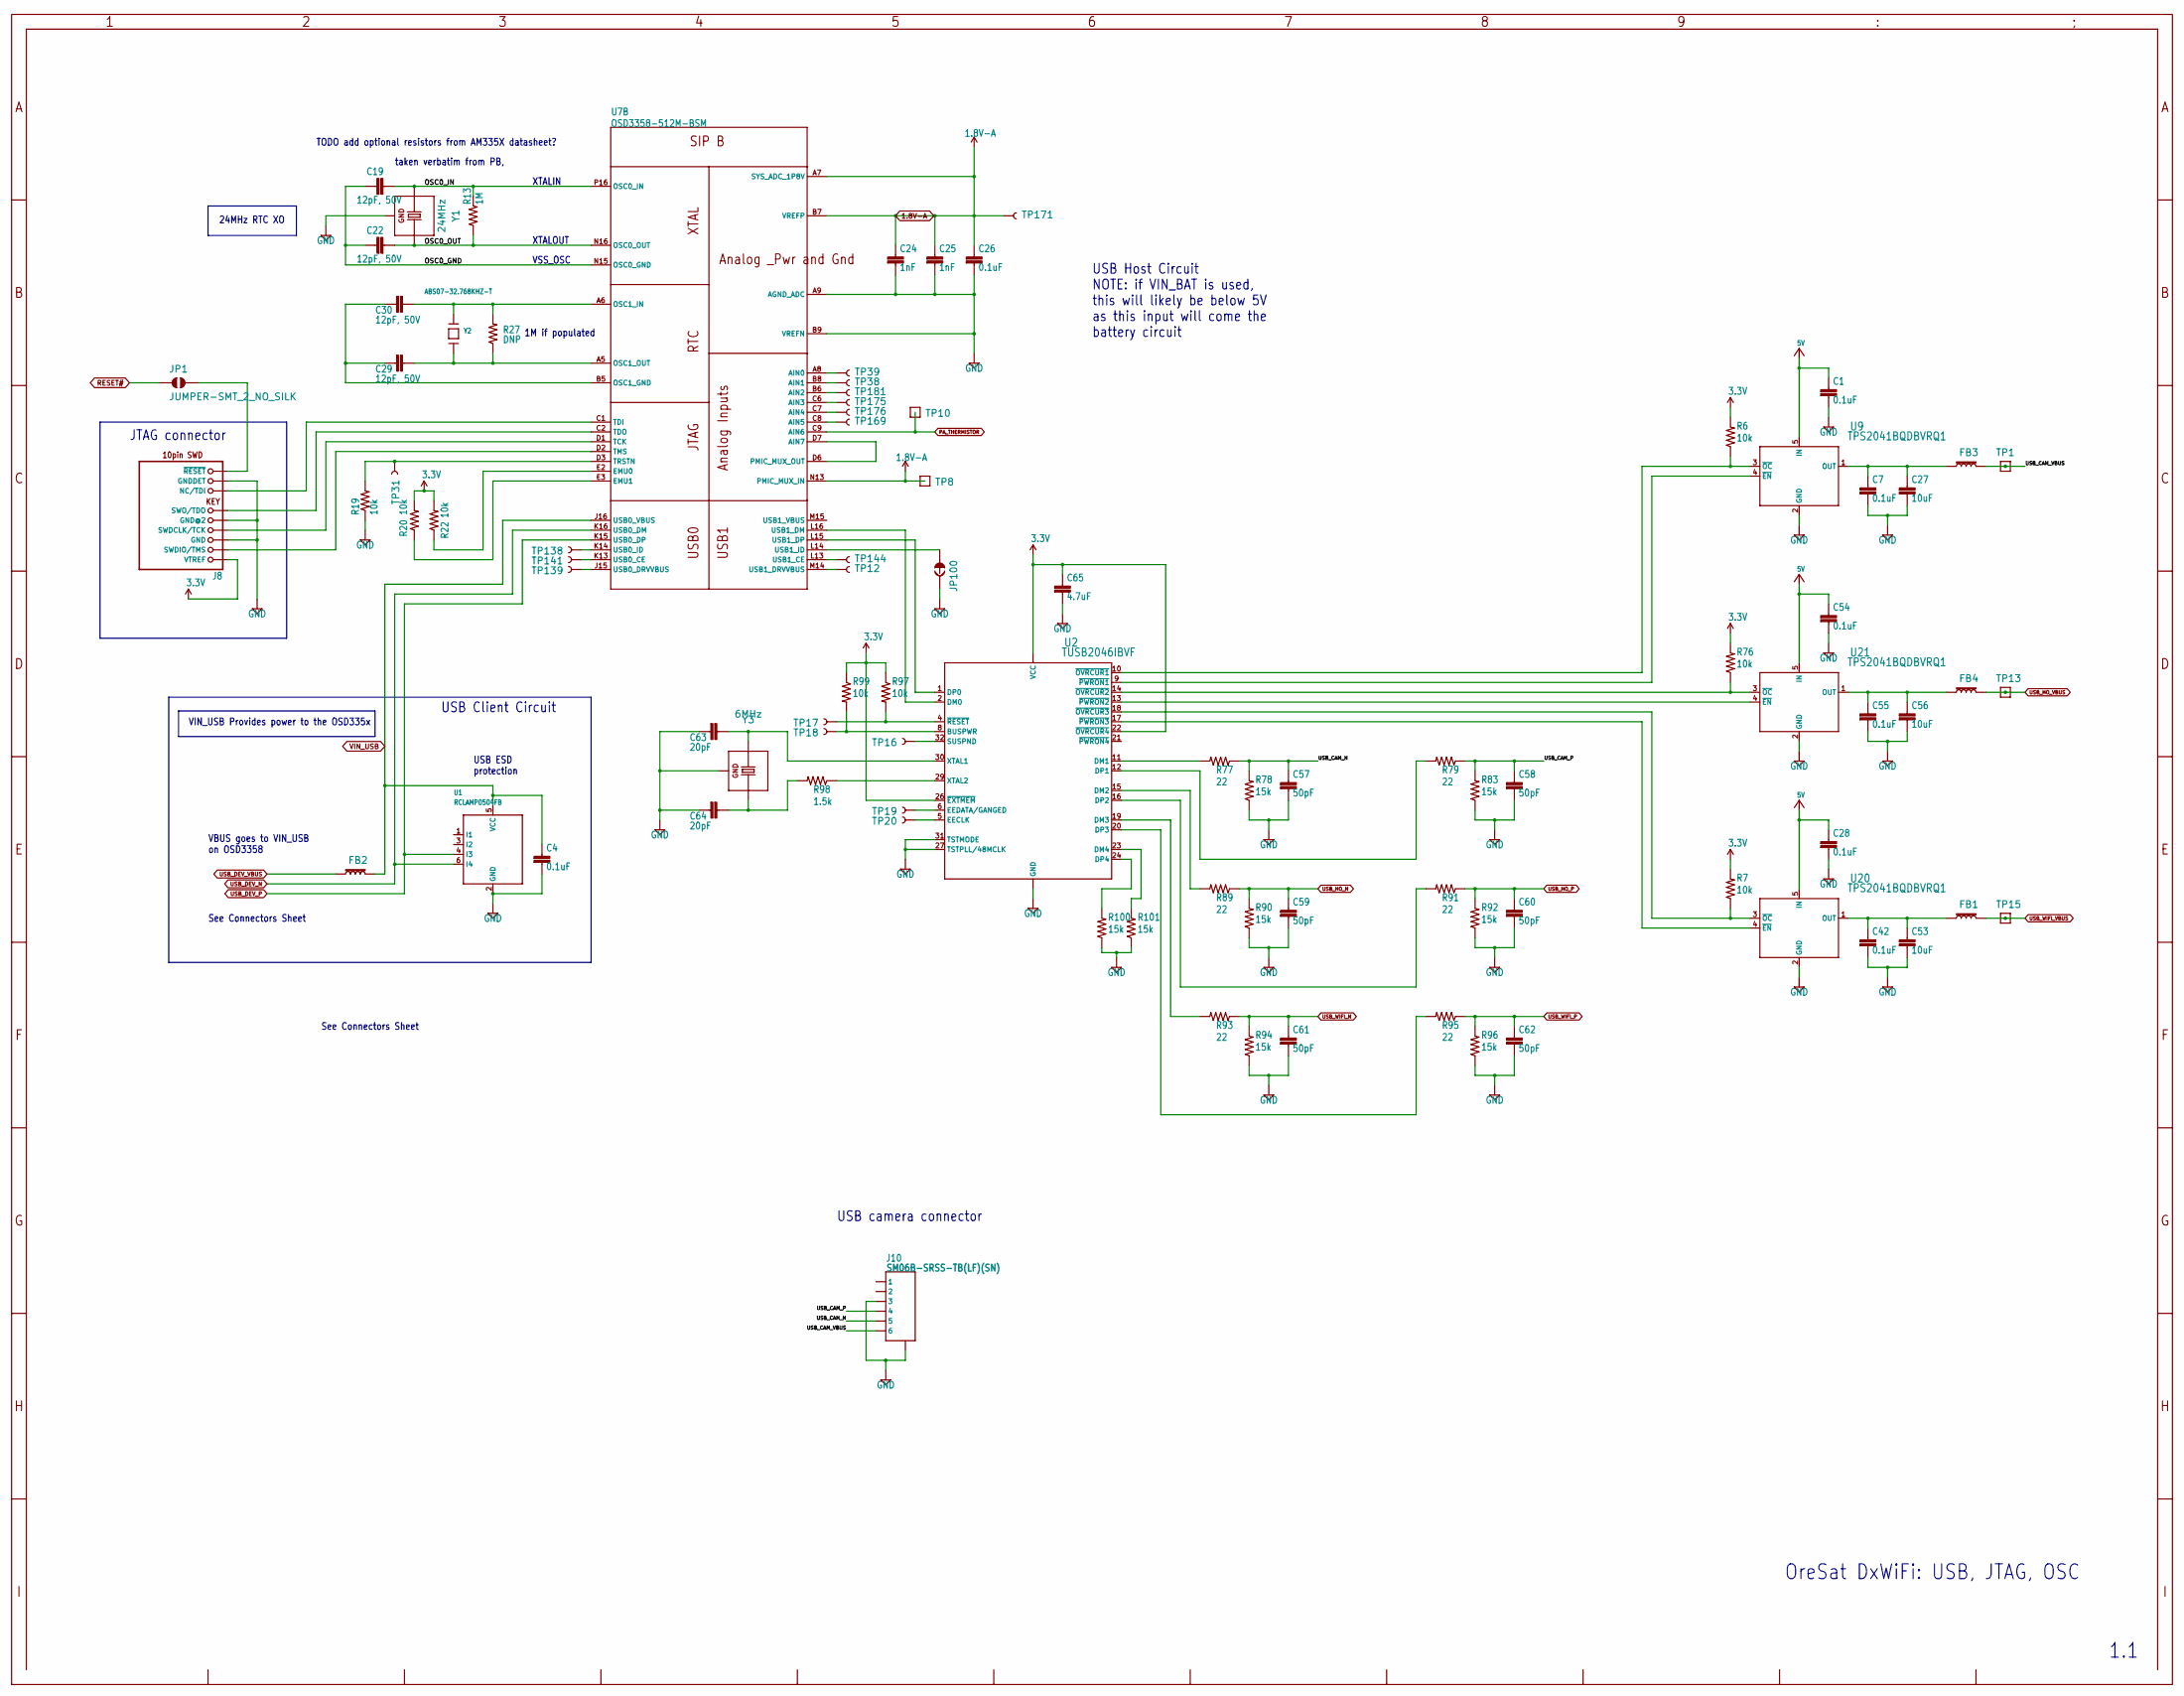
[picture p15: schematic OSD3358_USB,_JTAG,_XTAL,_etc_%3a_SIP_B.kicad_sch]

Parts:
C1, C4, C7, C28, C42, C54, C55: 0.1uF; .0603-A
C19, C22, C29, C30: 12pF, 50V; .0603-A
C24, C25: 1nF; .0805-B
C26: 0.1uF; .0805-B
C27, C53, C56: 10uF; .0603-A
C57, C58, C59, C60, C61, C62: 50pF; .0603-A
C63, C64: 20pF; .0603-A
C65: 4.7uF; .0603-A
FB1, FB2, FB3, FB4: BLM18KG300JH1D; 0603
J8: FTSH-105-XX-X-DV-K; CON10_2X5_DUK_FTSH
J10: SM06B-SRSS-TB(LF)(SN); CONN_SM06B-SRSS-TB_JST
JP1: JUMPER-SMT_2_NO_SILK; SMT-JUMPER_2_NO_SILK
JP100: JUMPER-SMT_2_NC_TRACE_SILK; SMT-JUMPER_2_NC_TRACE_SILK
R6, R7, R19, R20, R22, R76, R97, R99: 10k; .0603-A
R13: 1M; .0603-A
R27: DNP; .0603-A
R77, R79, R89, R91, R93, R95: 22; .0603-A
R78, R83, R90, R92, R94, R96, R100, R101: 15k; .0603-A
R98: 1.5k; .0603-A
TP1, TP8, TP10, TP13, TP15: TEST-POINT; 2MM-TEST-POINT
TP12, TP16, TP17, TP18, TP19, TP20, TP31, TP38, TP39, TP138, TP139, TP141, TP144, TP169, TP171, TP175, TP176, TP181: TEST-POINT3X4; PAD.03X.04
U1: RCLAMP0504FB; SC70-6
U2: TUSB2046IBVF; QFP80P900X900X160-32N
U7: OSD3358-512M-BSM; OSD335X-BGA-256
U9, U20, U21: TPS2041BQDBVRQ1; DBV5
Y1: 24MHz; 5X3.2-4SMD
Y2: ABS07-32.768KHZ-T; CRYSTAL_3.2X1.5
Y3: 6MHz; ECS_ECS-060-18-20BM-JEN-TR

Connections:
1.8V-A: C24.1, C25.1, C26.1, TP8.1, TP171.1, U7.A7 (SYS_ADC_1P8V), U7.B7 (VREFP), U7.N13 (PMIC_MUX_IN)
3.3V: C65.1, J8.1 (VTREF), R6.2, R7.2, R20.2, R22.2, R76.2, R97.1, R99.1, U2.3 (VCC), U2.22 (~OVRCUR4), U2.25 (VCC), U2.26 (~EXTMEM)
5V: C1.1, C28.1, C54.1, U9.5 (IN), U20.5 (IN), U21.5 (IN)
GND: C1.2, C4.2, C7.2, C24.2, C25.2, C26.2, C27.2, C28.2, C42.2, C53.2, C54.2, C55.2, C56.2, C57.2, C58.2, C59.2, C60.2, C61.2, C62.2, C63.2, C64.2, C65.2, J8.3 (GND), J8.5 (GND@2), J8.9 (GNDDET), J10.3, J10.7, J10.8 (7), JP100.2, R19.1, R78.1, R83.1, R90.1, R92.1, R94.1, R96.1, R100.1, R101.1, U1.2 (GND), U2.7 (GND), U2.27 (TSTPLL/48MCLK), U2.28 (GND), U2.31 (TSTMODE), U7.A9 (AGND_ADC), U7.B9 (VREFN), U9.2 (GND), U20.2 (GND), U21.2 (GND), Y1.2 (GND), Y1.4 (GND), Y3.2 (GND), Y3.4 (GND)
unnamed: C7.1, C27.1, FB3.1, U9.1 (OUT)
unnamed: C29.1, R27.1, U7.A5 (OSC1_OUT), Y2.P$1
unnamed: C29.2, C30.2, U7.B5 (OSC1_GND)
unnamed: C30.1, R27.2, U7.A6 (OSC1_IN), Y2.P$2
unnamed: C42.1, C53.1, FB1.1, U20.1 (OUT)
unnamed: C55.1, C56.1, FB4.1, U21.1 (OUT)
unnamed: C63.1, U2.30 (XTAL1), Y3.3 (X1)
unnamed: C64.1, R98.2, Y3.1 (X2)
unnamed: J8.2 (SWDIO/TMS), U7.D2 (TMS)
unnamed: J8.4 (SWDCLK/TCK), U7.D1 (TCK)
unnamed: J8.6 (SWO/TDO), U7.C2 (TDO)
unnamed: J8.8 (NC/TDI), U7.C1 (TDI)
unnamed: J8.10 (~RESET), JP1.2
unnamed: JP100.1, U7.L14 (USB1_ID)
unnamed: R6.1, U2.10 (~OVRCUR1), U9.3 (~OC)
unnamed: R7.1, U2.18 (~OVRCUR3), U20.3 (~OC)
unnamed: R19.2, TP31.1, U7.D3 (TRSTN)
unnamed: R20.1, U7.E3 (EMU1)
unnamed: R22.1, U7.E2 (EMU0)
unnamed: R76.1, U2.14 (~OVRCUR2), U21.3 (~OC)
unnamed: R77.2, U2.11 (DM1)
unnamed: R79.2, U2.12 (DP1)
unnamed: R89.2, U2.15 (DM2)
unnamed: R91.2, U2.16 (DP2)
unnamed: R93.2, U2.19 (DM3)
unnamed: R95.2, U2.20 (DP3)
unnamed: R97.2, TP17.1, U2.4 (~RESET)
unnamed: R98.1, U2.29 (XTAL2)
unnamed: R99.2, TP18.1, U2.8 (BUSPWR)
unnamed: R100.2, U2.24 (DP4)
unnamed: R101.2, U2.23 (DM4)
unnamed: TP12.1, U7.M14 (USB1_DRVVBUS)
unnamed: TP16.1, U2.32 (SUSPND)
unnamed: TP19.1, U2.6 (EEDATA/GANGED)
unnamed: TP20.1, U2.5 (EECLK)
unnamed: TP38.1, U7.B8 (AIN1)
unnamed: TP39.1, U7.A8 (AIN0)
unnamed: TP138.1, U7.K14 (USB0_ID)
unnamed: TP139.1, U7.J15 (USB0_DRVVBUS)
unnamed: TP141.1, U7.K13 (USB0_CE)
unnamed: TP144.1, U7.L13 (USB1_CE)
unnamed: TP169.1, U7.C8 (AIN5)
unnamed: TP175.1, U7.C6 (AIN3)
unnamed: TP176.1, U7.C7 (AIN4)
unnamed: TP181.1, U7.B6 (AIN2)
unnamed: U2.1 (DP0), U7.L15 (USB1_DP)
unnamed: U2.2 (DM0), U7.L16 (USB1_DM)
unnamed: U2.9 (~PWRON1), U9.4 (~EN)
unnamed: U2.13 (~PWRON2), U21.4 (~EN)
unnamed: U2.17 (~PWRON3), U20.4 (~EN)
unnamed: U7.D6 (PMIC_MUX_OUT), U7.D7 (AIN7)
OSC0_GND: C19.1, C22.1, U7.N15 (OSC0_GND)
OSC0_IN: C19.2, R13.2, U7.P16 (OSC0_IN), Y1.1 (X1)
OSC0_OUT: C22.2, R13.1, U7.N16 (OSC0_OUT), Y1.3 (X2)
PA_THERMISTOR: TP10.1, U7.C9 (AIN6)
RESET#: JP1.1
USB_CAM_N: C57.1, J10.5, R77.1, R78.2
USB_CAM_P: C58.1, J10.4, R79.1, R83.2
USB_CAM_VBUS: FB3.2, J10.6, TP1.1
USB_DEV_N: U1.6 (I4), U7.K16 (USB0_DM)
USB_DEV_P: U1.4 (I3), U7.K15 (USB0_DP)
USB_DEV_VBUS: FB2.1
USB_HO_N: C59.1, R89.1, R90.2
USB_HO_P: C60.1, R91.1, R92.2
USB_HO_VBUS: FB4.2, TP13.1
USB_WIFI_N: C61.1, R93.1, R94.2
USB_WIFI_P: C62.1, R95.1, R96.2
USB_WIFI_VBUS: FB1.2, TP15.1
VIN_USB: C4.1, FB2.2, U1.5 (VCC), U7.J16 (USB0_VBUS)

Notes on the sheet:
See Connectors Sheet
USB ESD protection
USB Host Circuit NOTE: if VIN_BAT is used, this will likely be below 5V as this input will come the battery circuit
TODO add optional resistors from AM335X datasheet?
24MHz RTC XO
taken verbatim from PB,
XTALOUT
1M if populated
JTAG connector
XTALIN
VSS_OSC
USB camera connector
VIN_USB Provides power to the OSD335x
1.1
VBUS goes to VIN_USB on OSD3358
USB Client Circuit
OreSat DxWiFi: USB, JTAG, OSC
