oresat/oresat-proto-card/a8-proto-card/cad-files/Power.kicad_sch

## KiCad design a8-proto-card/cad-files/Power.kicad_sch (2021-11-15)

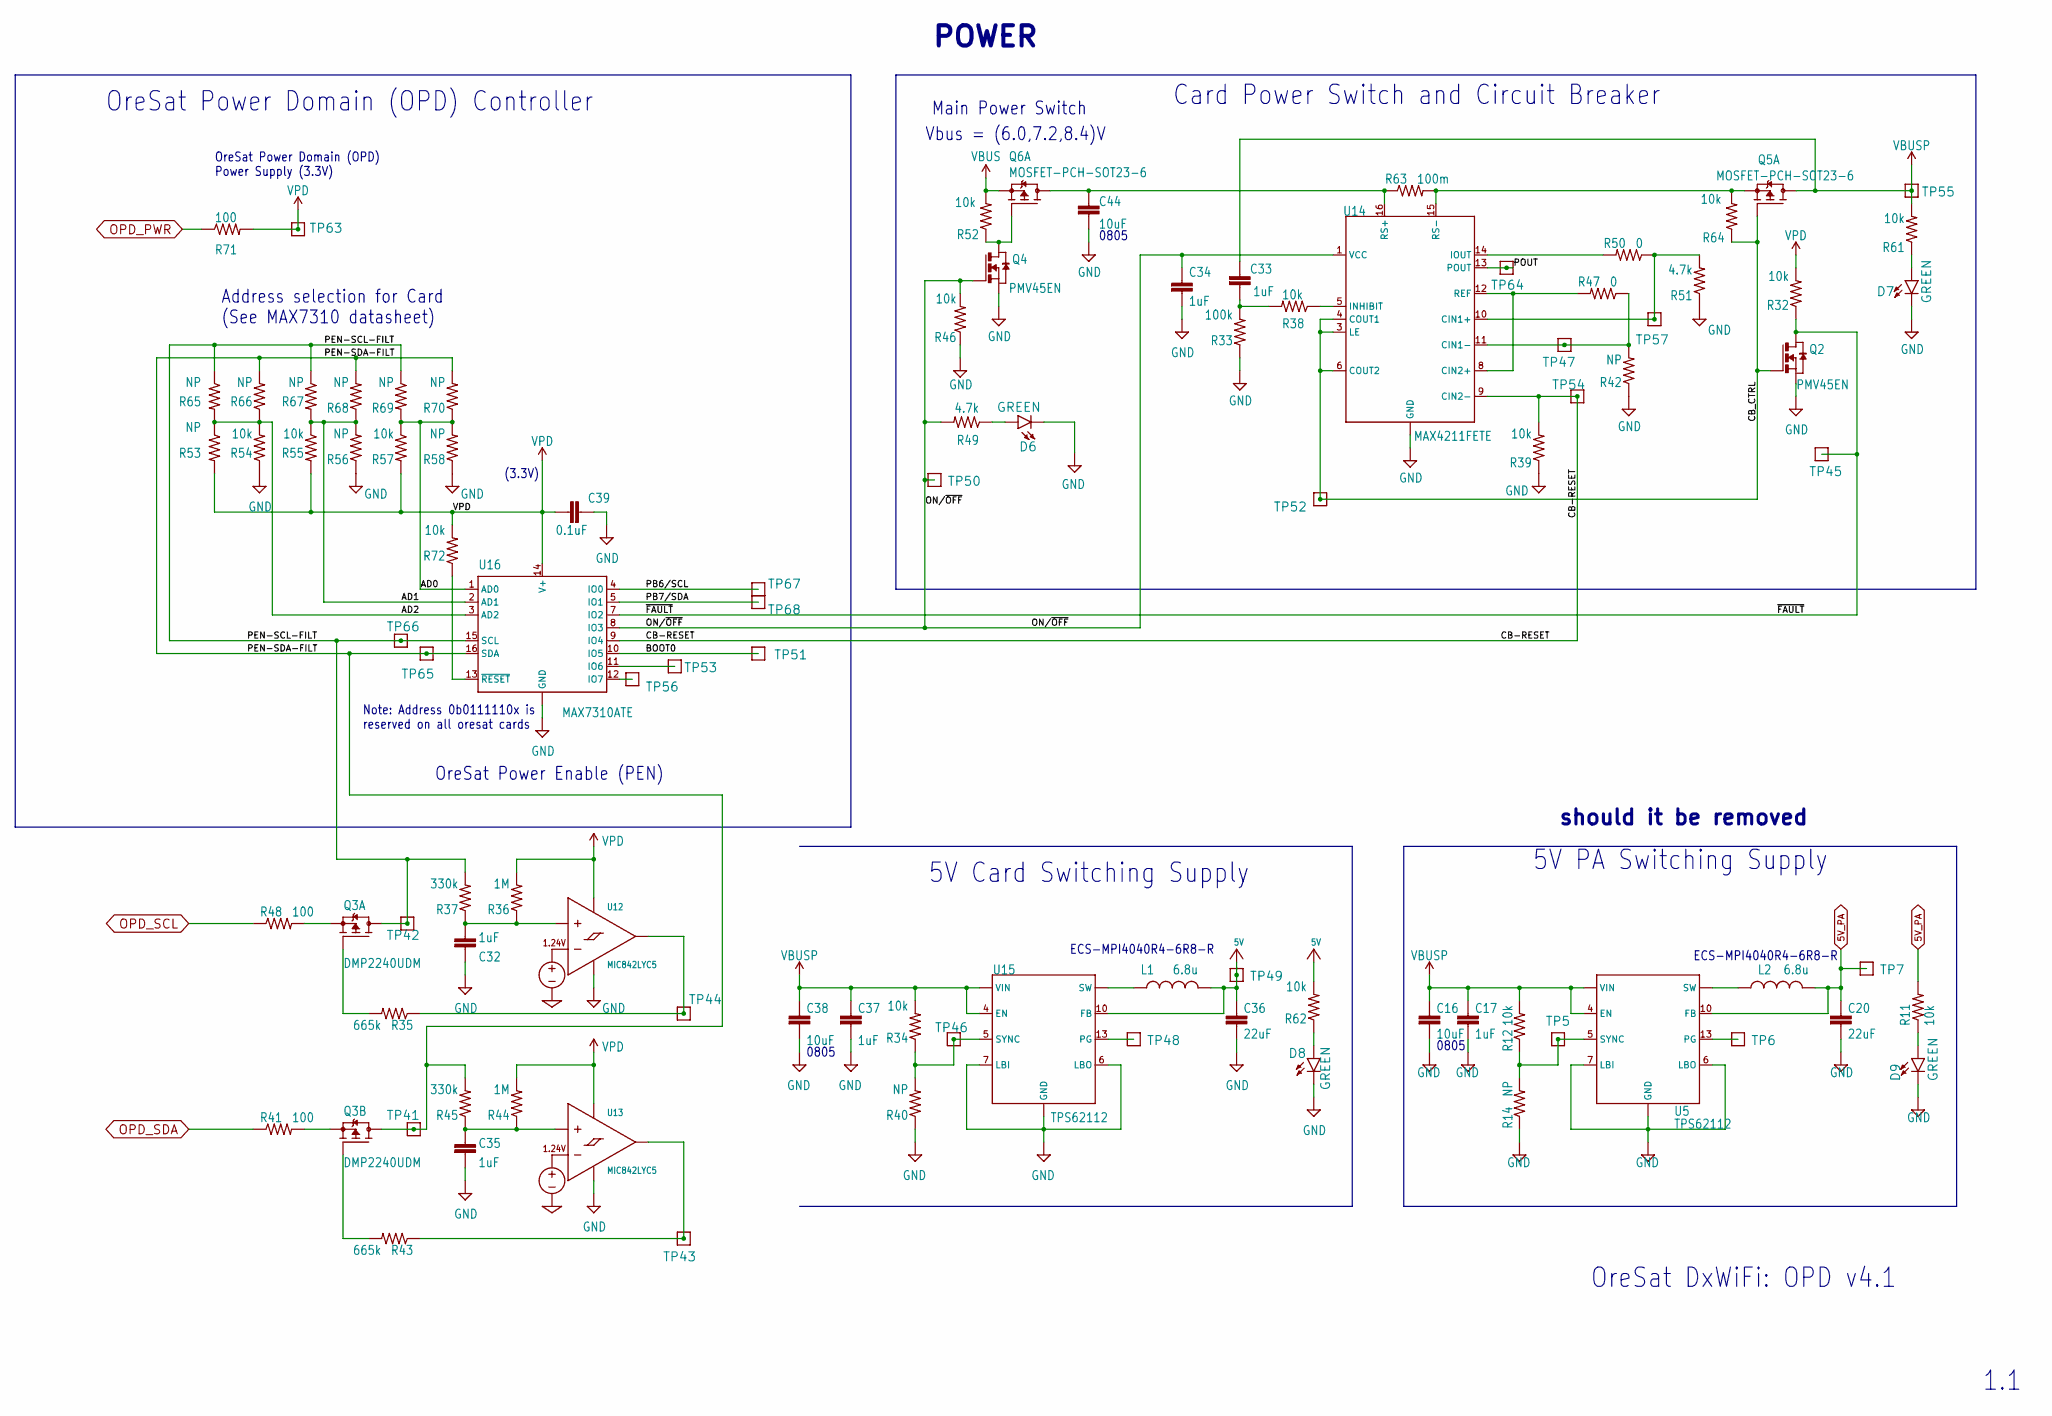
[picture p16: schematic Power.kicad_sch]

Parts:
C16, C38, C44: 10uF; .0805-B
C17, C34, C37: 1uF; .0603-A
C20: GCJ32ER71C226KE01L; C1210
C32, C35: 1uF; .0805-B-NOSILK
C33: CL05B104KO5NNNC; .0603-A
C36: 22uF; C1210
C39: 0.1uF; .0603-A
D6, D7, D8, D9: 150060VS55040; LED-0603
L1, L2: 6.8u; ECS-MPI4040
Q2, Q4: PMV45EN2R; SOT23
Q3: DMP2240UDM; SOT23-6
Q5, Q6: DMP3050LVT-7; SOT23-6
R11, R12, R32, R34, R39, R46, R52, R61, R62, R64, R72: 10k; .0603-A
R14, R33, R38, R40, R42, R51, R53, R54, R55, R56, R57, R58, R65, R66, R67, R68, R69, R70: RC1005F6653CS; .0603-A
R35, R43: 665k; .0603-A
R36, R44: 1M; .0603-A
R37, R45: 330k; .0603-A
R41, R48, R71: 100; .0603-A
R47, R50: 0; .0603-A
R49: 4.7k; .0603-A
R63: 100m; R1206
TP5, TP6, TP7, TP41, TP42, TP43, TP44, TP45, TP46, TP47, TP48, TP49, TP50, TP51, TP52, TP53, TP54, TP55, TP56, TP57, TP63, TP64, TP65, TP66, TP67, TP68: TEST-POINT; 2MM-TEST-POINT
U5, U15: TPS62112; S-PVQFN-16
U12, U13: MIC842LYC5; SC70-5
U14: MAX4211FETE; QFN65P400X400X80-17T210
U16: MAX7310ATE; QFN65P400X400X80-17T210

Connections:
5V: C36.1, L1.2, R62.2, TP49.1, U15.10 (FB)
5V_PA: C20.1, L2.2, R11.2, TP7.1, U5.10 (FB)
AD0: R57.1, R58.2, R69.2, R70.1, U16.1 (AD0)
AD1: R55.1, R56.2, R67.2, R68.1, U16.2 (AD1)
AD2: R53.1, R54.2, R65.2, R66.1, U16.3 (AD2)
BOOT0: TP51.1, U16.10 (IO5)
CB-RESET: R39.2, TP54.1, U14.9 (CIN2-), U16.9 (IO4)
CB_CTRL: Q2.1 (G), Q5.1 (G), R64.1, TP52.1, U14.3 (LE), U14.4 (COUT1), U14.6 (COUT2)
GND: C16.2, C17.2, C20.2, C32.2, C34.2, C35.2, C36.2, C37.2, C38.2, C39.1, C44.2, D6.C, D7.C, D8.C, D9.C, Q2.2 (S), Q4.2 (S), R14.1, R33.1, R39.1, R40.1, R42.1, R46.1, R51.1, R54.1, R56.1, R58.1, U5.1 (GND), U5.6 (LBO), U5.7 (LBI), U5.9 (GND), U5.11 (GND), U5.12 (GND), U5.16 (GND), U5.PAD (GND), U12.2 (GND), U13.2 (GND), U14.7 (GND), U14.EPAD (GND), U15.1 (GND), U15.6 (LBO), U15.7 (LBI), U15.9 (GND), U15.11 (GND), U15.12 (GND), U15.16 (GND), U15.PAD (GND), U16.6 (GND), U16.EPAD (GND)
unnamed: C32.1, R36.1, R37.1, U12.1 (INP)
unnamed: C33.1, R33.2, R38.2
unnamed: C35.1, R44.1, R45.1, U13.1 (INP)
unnamed: C44.1, Q6.6 (D), R63.1, U14.16 (RS+)
unnamed: D6.A, R49.1
unnamed: D7.A, R61.1
unnamed: D8.A, R62.1
unnamed: D9.A, R11.1
unnamed: L1.1, U15.14 (SW), U15.15 (SW)
unnamed: L2.1, U5.14 (SW), U5.15 (SW)
unnamed: Q3.1 (G), R35.2
unnamed: Q3.2 (S), R41.2
unnamed: Q3.3 (G), R43.2
unnamed: Q3.5 (S), R48.2
unnamed: Q4.3 (D), Q6.1 (G), R52.1
unnamed: Q5.5 (S), R63.2, R64.2, U14.15 (RS-)
unnamed: R12.1, R14.2, TP5.1, U5.5 (SYNC)
unnamed: R34.1, R40.2, TP46.1, U15.5 (SYNC)
unnamed: R35.1, TP44.1, U12.4 (OUT)
unnamed: R38.1, U14.5 (INHIBIT)
unnamed: R42.2, R47.1, TP47.1, U14.11 (CIN1-)
unnamed: R43.1, TP43.1, U13.4 (OUT)
unnamed: R47.2, U14.8 (CIN2+), U14.12 (REF)
unnamed: R50.1, R51.2, TP57.1, U14.10 (CIN1+)
unnamed: R50.2, U14.14 (IOUT)
unnamed: R72.1, U16.13 (~RESET)
unnamed: TP6.1, U5.13 (PG)
unnamed: TP48.1, U15.13 (PG)
unnamed: TP53.1, U16.11 (IO6)
unnamed: TP56.1, U16.12 (IO7)
ON/~OFF: C34.1, Q4.1 (G), R46.2, R49.2, TP50.1, U14.1 (VCC), U16.8 (IO3)
OPD_PWR: R71.1
OPD_SCL: R48.1
OPD_SDA: R41.1
PB6/SCL: TP67.1, U16.4 (IO0)
PB7/SDA: TP68.1, U16.5 (IO1)
PEN-SCL-FILT: Q3.6 (D), R37.2, R65.1, R67.1, R69.1, TP42.1, TP66.1, U16.15 (SCL)
PEN-SDA-FILT: Q3.4 (D), R45.2, R66.2, R68.2, R70.2, TP41.1, TP65.1, U16.16 (SDA)
POUT: TP64.1, U14.13 (POUT)
VBUS: Q6.5 (S), R52.2
VBUSP: C16.1, C17.1, C33.2, C37.1, C38.1, Q5.6 (D), R12.2, R34.2, R61.2, TP55.1, U5.2 (VIN), U5.3 (VIN), U5.4 (EN), U5.8 (VIN), U15.2 (VIN), U15.3 (VIN), U15.4 (EN), U15.8 (VIN)
VPD: C39.2, R32.2, R36.2, R44.2, R53.2, R55.2, R57.2, R71.2, R72.2, TP63.1, U12.5 (VDD), U13.5 (VDD), U16.14 (V+)
~FAULT: Q2.3 (D), R32.1, TP45.1, U16.7 (IO2)

Notes on the sheet:
POWER
ECS-MPI4040R4-6R8-R
OreSat Power Domain (OPD) Controller
Note: Address 0b0111110x is reserved on all oresat cards
(3.3V)
5V Card Switching Supply
5V PA Switching Supply
OreSat DxWiFi: OPD v4.1
0805
1.1
Main Power Switch
Address selection for Card (See MAX7310 datasheet)
should it be removed
Vbus = (6.0,7.2,8.4)V
Card Power Switch and Circuit Breaker
OreSat Power Domain (OPD) Power Supply (3.3V)
OreSat Power Enable (PEN)
