oresat/oresat-proto-card/a8-proto-card/cad-files/oresat-live-card_6.kicad_sch

## KiCad design a8-proto-card/cad-files/oresat-live-card_6.kicad_sch (2021-11-11)

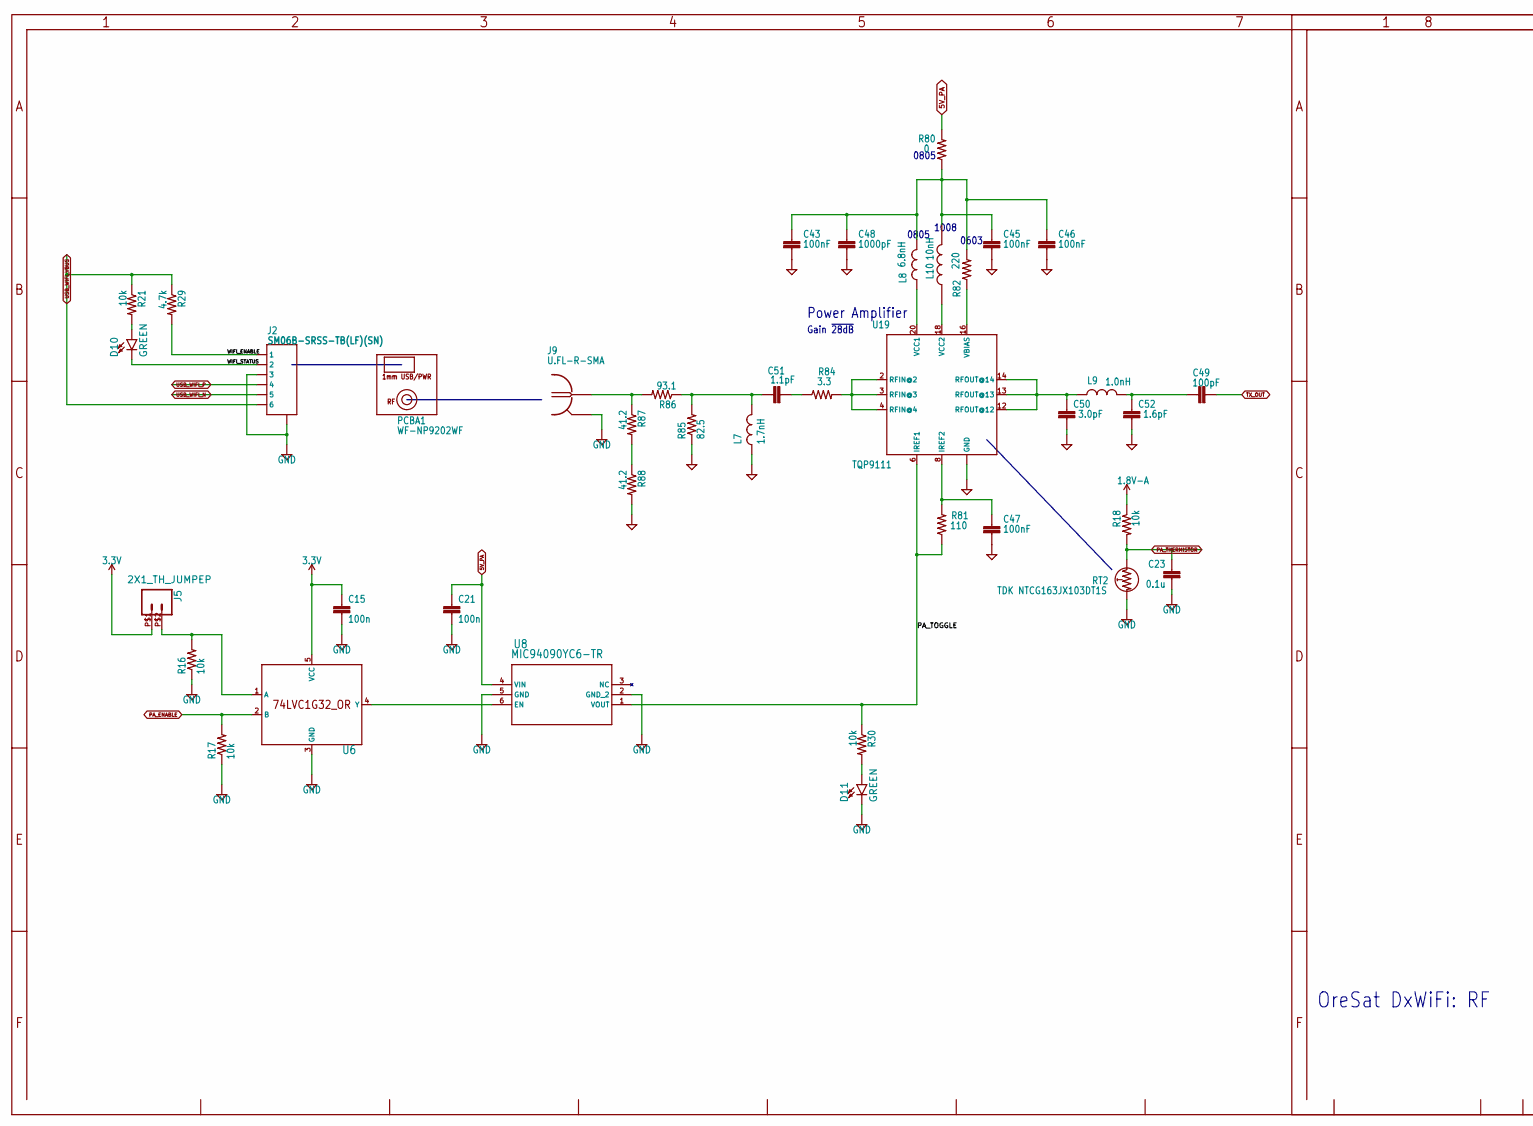
[picture p17: schematic oresat-live-card_6.kicad_sch, part in row 1, column 1]

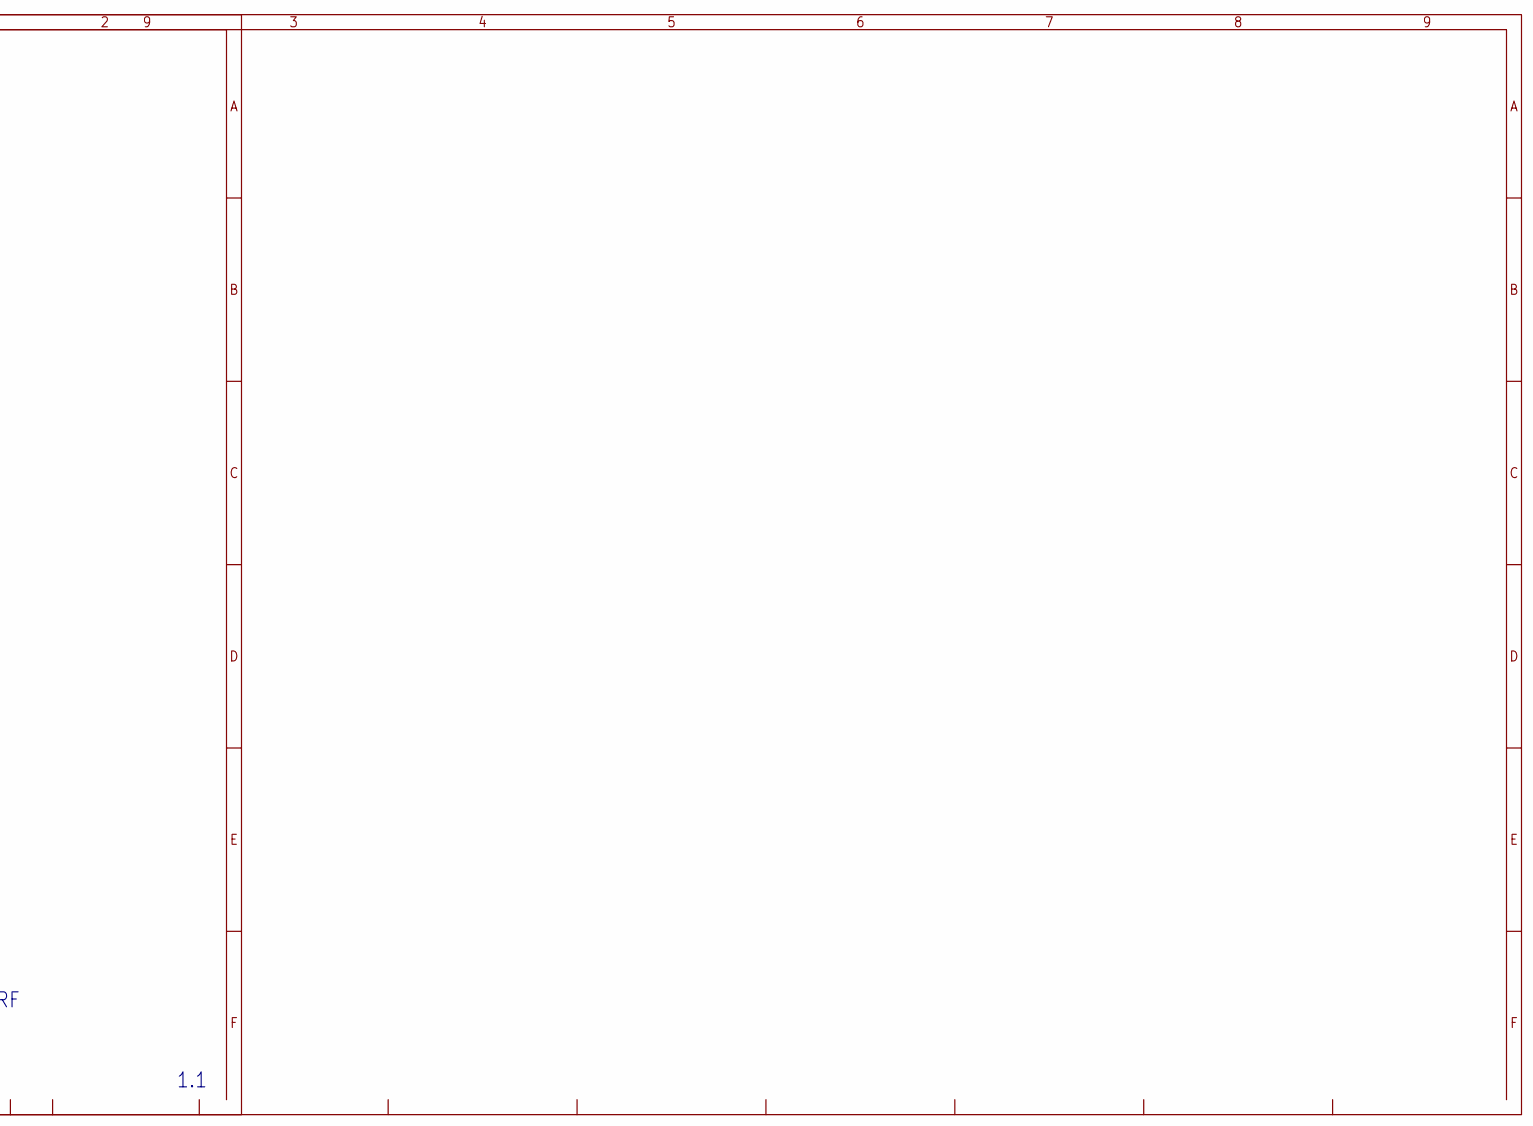
[picture p18: schematic oresat-live-card_6.kicad_sch, part in row 1, column 2]

Parts:
C15, C21: 100n; .0603-A
C23: 0.1u; .0603-A
C43, C45, C46: CGA2B1X7R1C104K050BC; .0402-B-NOSILK
C47: CGA2B1X7R1C104K050BC; .0402-C-NOSILK
C48: CGA2B2NP01H102J050BA; .0402-B-NOSILK
C49: GCM1885C1H101JA16D; .0402-C-NOSILK
C50: 04025U3R0BAT2A; .0402-C-NOSILK
C51: 04025J1R1PBSTR\500; .0402-C-NOSILK
C52: 04025U1R6BAT2A; .0402-C-NOSILK
D10, D11: 150060VS55040; LED-0603
J2: SM06B-SRSS-TB(LF)(SN); CONN_SM06B-SRSS-TB_JST
J5: 2X1_TH_JUMPEP; 2X1
J9: U.FL-R-SMA; U.FL-R-SMT
L7: 0402DC-1N7XJRU; .0402-C-NOSILK
L8: 0805CS-060XJLC; .0805-C-NOSILK
L9: MLK1005S1N0ST000; .0402-C-NOSILK
L10: Fixed Inductors 1008 10nH Unshld 5% 1.6A 60mOhms; INDC2928X203N
PCBA1: WF-NP9202WF; WF-NP9202
R16, R17, R18, R21, R30: 10k; .0603-A
R29: 4.7k; .0603-A
R80: ERJ-6GEY0R00V; R0805
R81: ERJ-2RKF1100X; .0402-B-NOSILK
R82: ERJ-3EKF2200V; .0603-C-NOSILK
R84: CRCW04023R30FKED; .0402-C-NOSILK
R85: ERJ-3EKF82R5V; .0603-A
R86: ERJ-3EKF93R1V; .0603-A
R87, R88: ERJ-3EKF41R2V; .0603-A
RT2: TDK NTCG163JX103DT1S; 0603-THERMISTOR-B
U6: SN74LVC1G32QDBVRQ1; DBV5
U8: MIC94090YC6-TR; SC-70-6_MCH
U19: TQP9111; QFN50P400X400X102-21N

Connections:
1.8V-A: R18.1
3.3V: C15.1, J5.P$1 (1), U6.5 (VCC)
5V_PA: C21.1, R80.2, U8.4 (VIN)
GND: C15.2, C21.2, C23.2, C43.2, C45.2, C46.2, C47.2, C48.2, C50.2, C52.2, D11.C, J2.3, J2.7, J2.8 (7), J9.2, J9.3, L7.1, R16.1, R17.1, R85.1, R88.2, RT2.2, U6.3 (GND), U8.2 (GND_2), U8.5 (GND), U19.1 (GND), U19.5 (GND), U19.7 (GND), U19.9 (GND), U19.10 (GND), U19.11 (GND), U19.15 (GND), U19.17 (GND), U19.19 (GND), U19.21 (GND)
unnamed: C43.1, C45.1, C46.1, C48.1, L8.2, L10.2, R80.1, R82.2
unnamed: C47.1, R81.2, U19.8 (IREF2)
unnamed: C49.1, C52.1, L9.2
unnamed: C50.1, L9.1, U19.12 (RFOUT@12), U19.13 (RFOUT@13), U19.14 (RFOUT@14)
unnamed: C51.1, L7.2, R85.2, R86.1
unnamed: C51.2, R84.1
unnamed: D10.A, R21.2
unnamed: D11.A, R30.2
unnamed: J5.P$2 (2), R16.2, U6.1 (A)
unnamed: J9.1, R86.2, R87.1
unnamed: L8.1, U19.20 (VCC1)
unnamed: L10.1, U19.18 (VCC2)
unnamed: R82.1, U19.16 (VBIAS)
unnamed: R84.2, U19.2 (RFIN@2), U19.3 (RFIN@3), U19.4 (RFIN@4)
unnamed: R87.2, R88.1
unnamed: U6.4 (Y), U8.6 (EN)
PA_ENABLE: R17.2, U6.2 (B)
PA_THERMISTOR: C23.1, R18.2, RT2.1
PA_TOGGLE: R30.1, R81.1, U8.1 (VOUT), U19.6 (IREF1)
TX_OUT: C49.2
USB_WIFI_N: J2.5
USB_WIFI_P: J2.4
USB_WIFI_VBUS: J2.6, R21.1, R29.1
WIFI_ENABLE: J2.1, R29.2
WIFI_STATUS: D10.C, J2.2

Notes on the sheet:
1008
0805
Power Amplifier
OreSat DxWiFi: RF
1.1
Gain ~{28dB}
0603
